KALTCHUK/Z80_Modular_Computer/CPM software/Wordstar/readme.md

## What you'll find in this directory ##
WordStar, an impressive word processor from MicroPro International Corporation. I use it extensively to write all the programs in C, BASIC and assembly language. WSU.COM is the unconfigured version of WordStar. WS.COM is the version I configured for use with VT-100 terminal, 40x80.
