KALTCHUK/Z80_Modular_Computer/CPM software/ZSID/readme.md

## What you'll find in this directory ##
ZSID - Z80 Simbolic Instruction Debugger, from Digital Research. Very useful to debug assembly programs. I used it several times and it saved me many hours. MAKESYM.COM is used to transform .LST file generated by Z80ASM into symbolic tables in a format that ZSID can understand.
