KALTCHUK/Z80_Modular_Computer/pics and vids/backplane_1.jpg

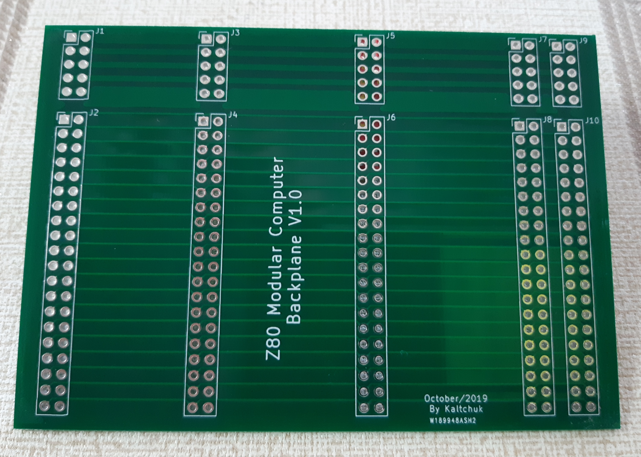
pics and vids/backplane_1.jpg
