KALTCHUK/Z80_Modular_Computer/pics and vids/backplane_3.jpg

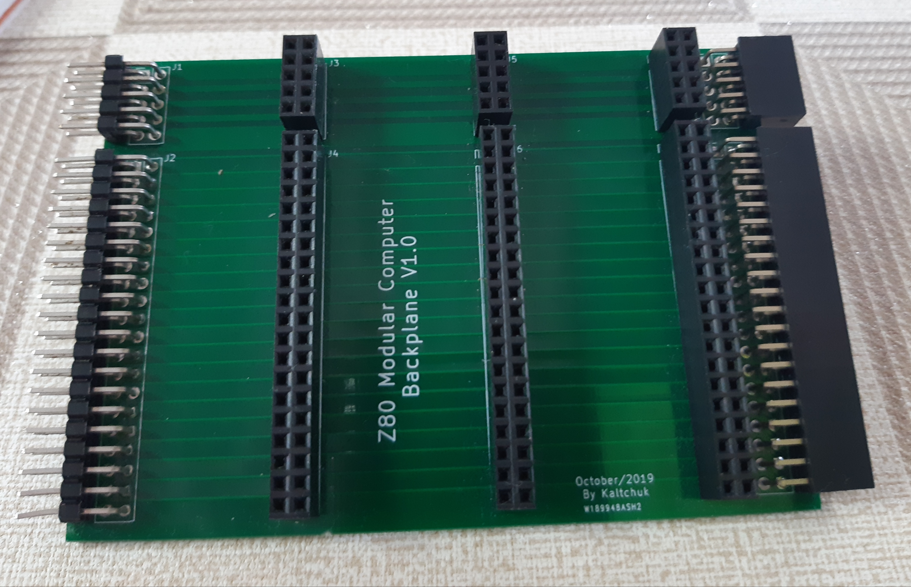
pics and vids/backplane_3.jpg
