KALTCHUK/Z80_Modular_Computer/pics and vids/eprog_1.jpg

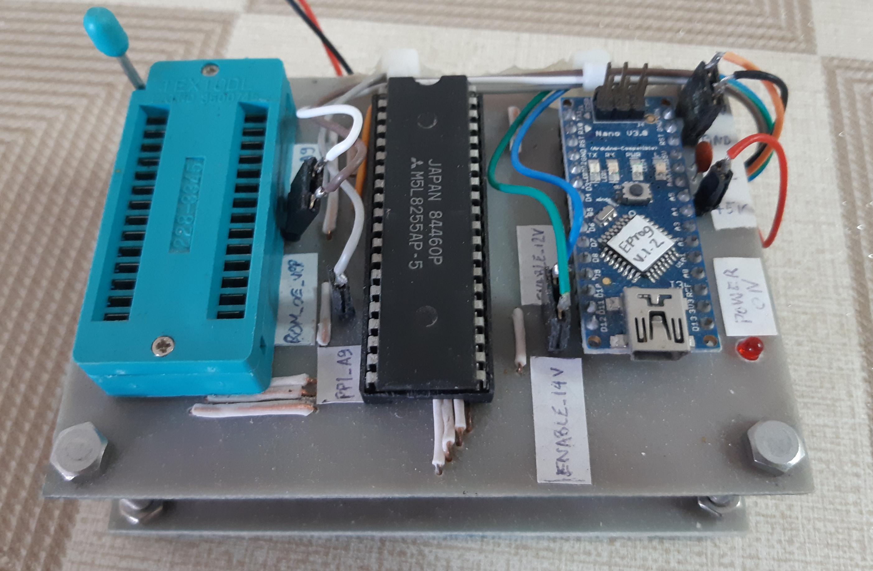
pics and vids/eprog_1.jpg
