KALTCHUK/Z80_Modular_Computer/pics and vids/eprog_2.jpg

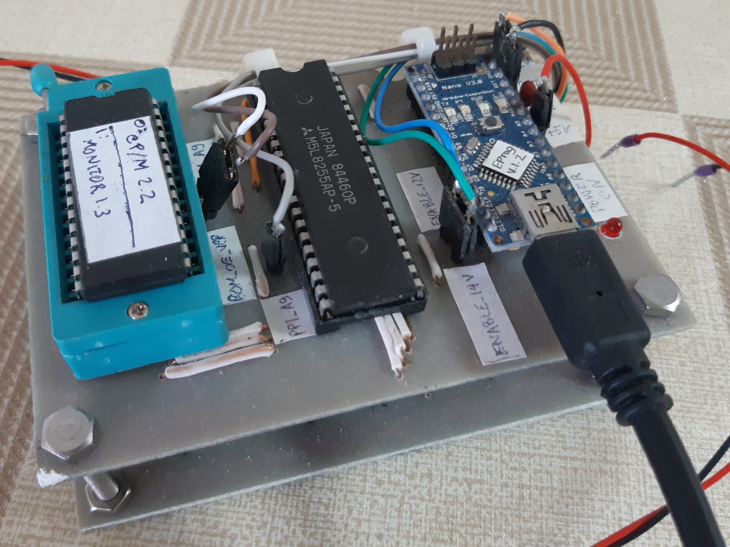
pics and vids/eprog_2.jpg
