KALTCHUK/Z80_Modular_Computer/pics and vids/MANDEL3.png

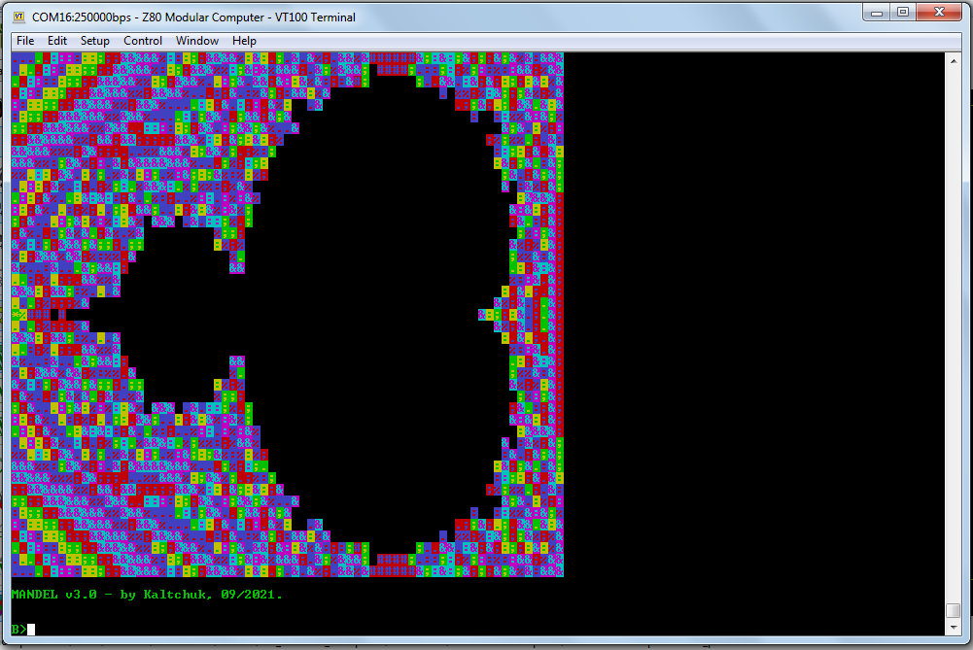
pics and vids/MANDEL3.png
