KALTCHUK/Z80_Modular_Computer/pics and vids/proto_cpu_1.jpg

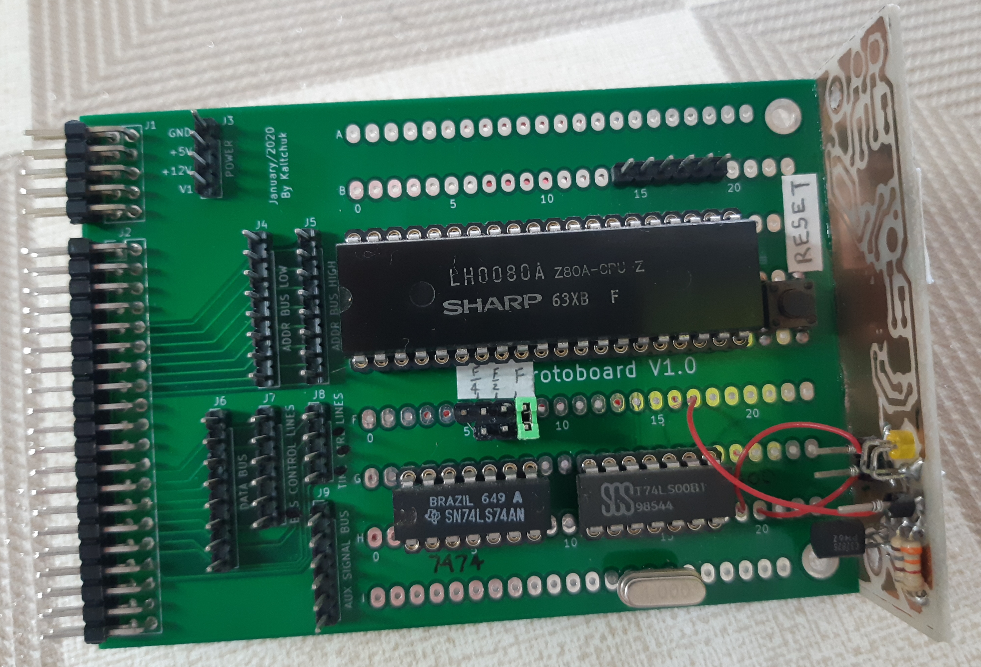
pics and vids/proto_cpu_1.jpg
