KALTCHUK/Z80_Modular_Computer/pics and vids/proto_flash_1.jpg

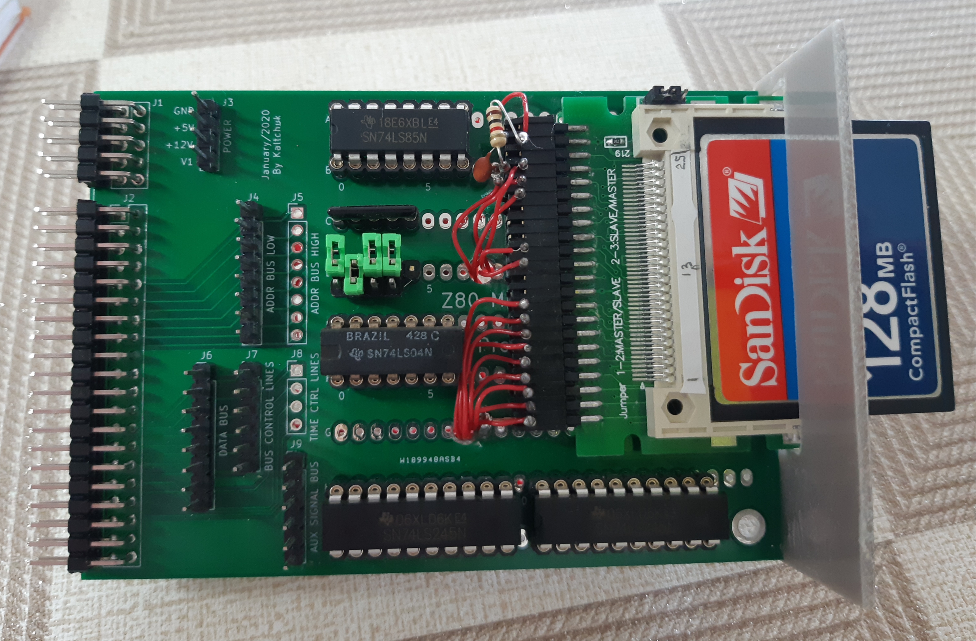
pics and vids/proto_flash_1.jpg
