KALTCHUK/Z80_Modular_Computer/pics and vids/proto_flash_3.jpg

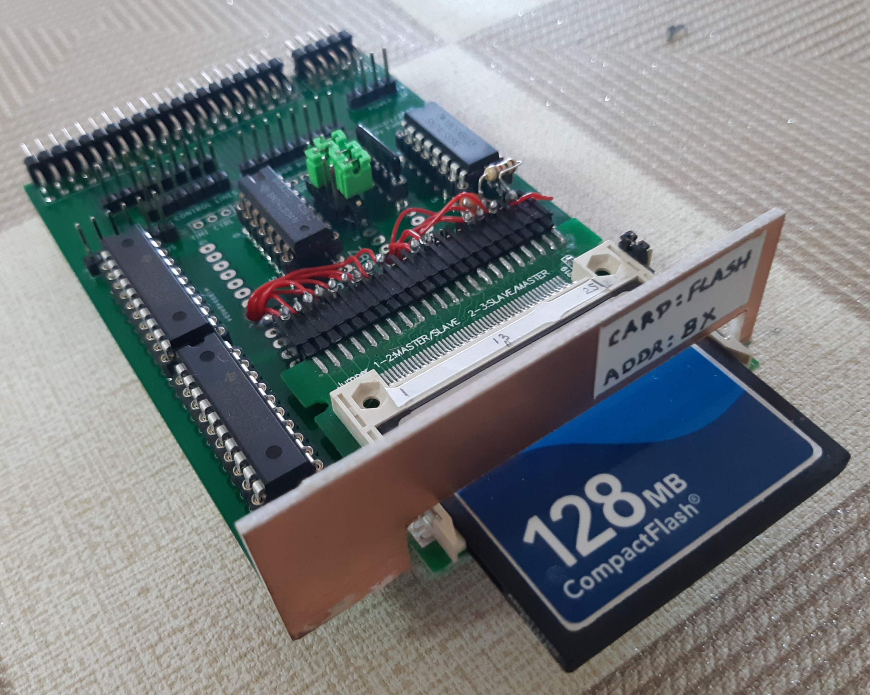
pics and vids/proto_flash_3.jpg
