KALTCHUK/Z80_Modular_Computer/pics and vids/proto_lcd_2.jpg

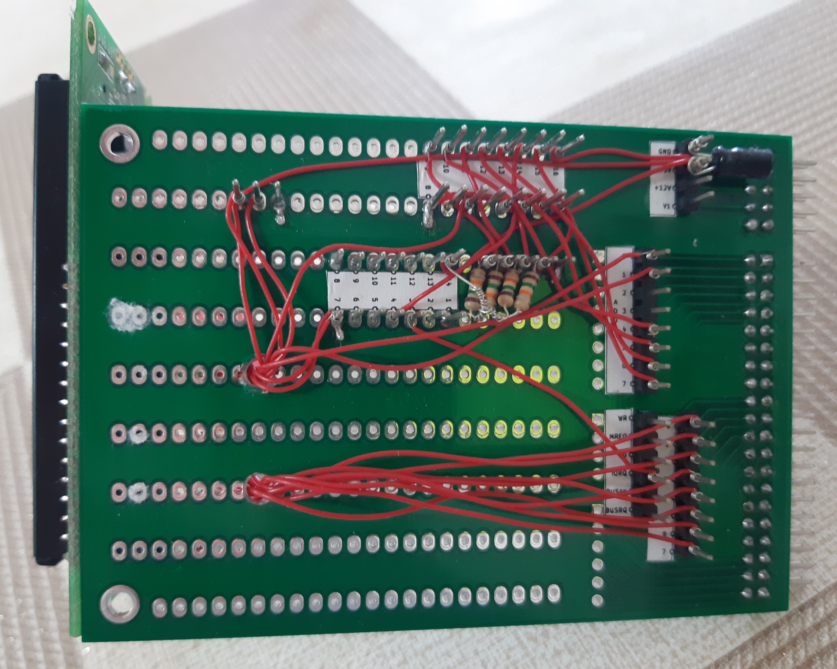
pics and vids/proto_lcd_2.jpg
