KALTCHUK/Z80_Modular_Computer/pics and vids/proto_lcd_3.jpg

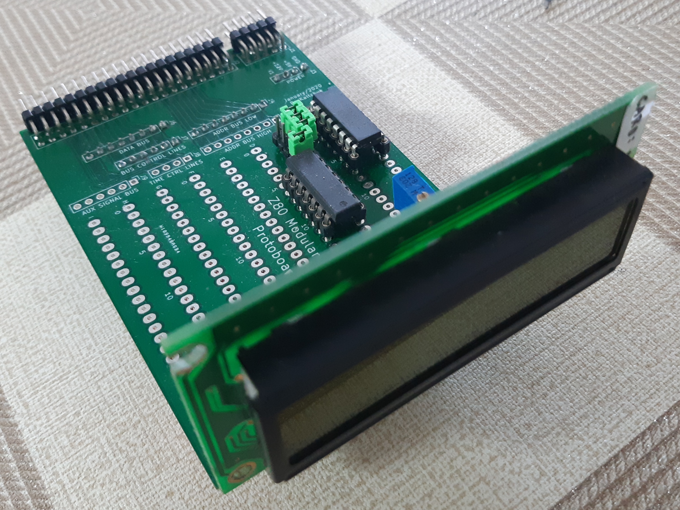
pics and vids/proto_lcd_3.jpg
