KALTCHUK/Z80_Modular_Computer/pics and vids/proto_mem_3.jpg

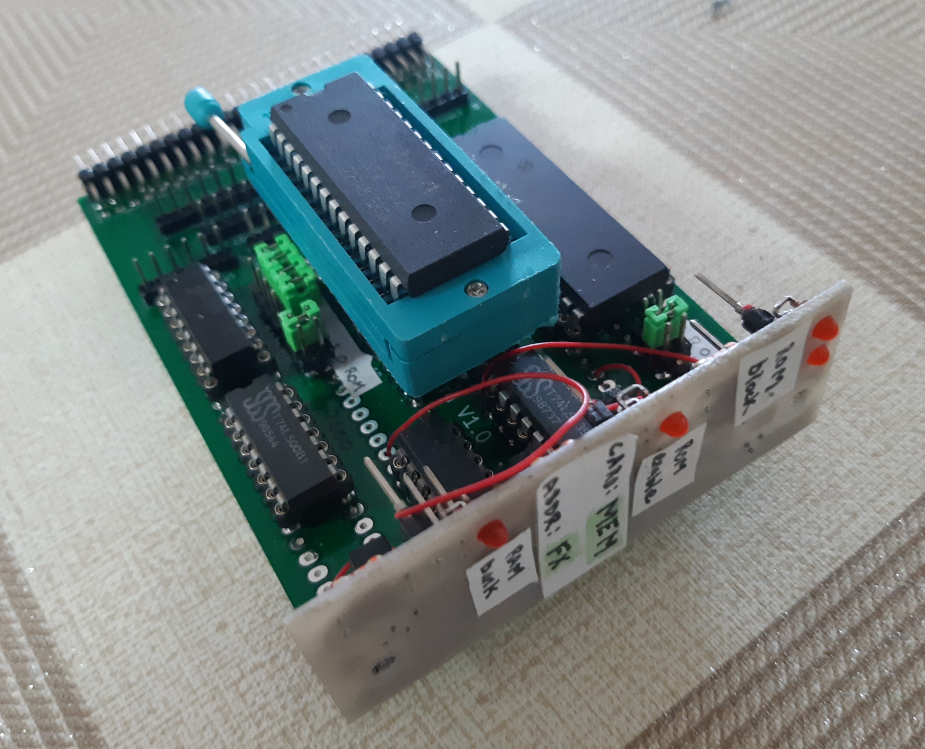
pics and vids/proto_mem_3.jpg
