KALTCHUK/Z80_Modular_Computer/pics and vids/proto_usart_2.jpg

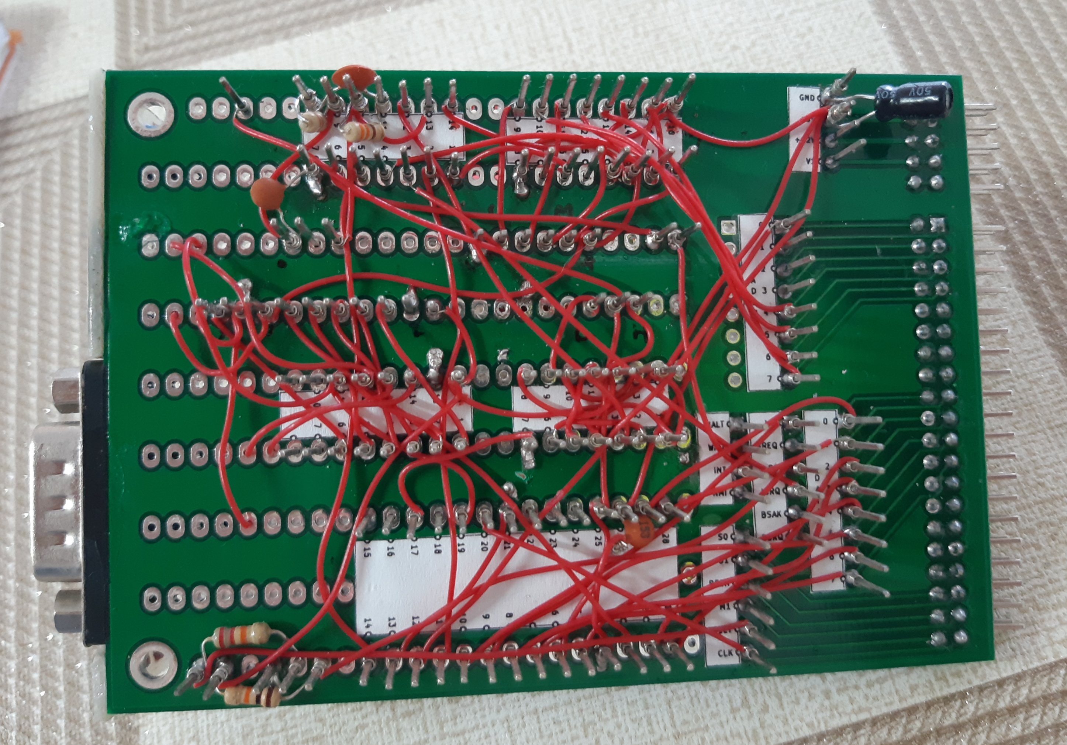
pics and vids/proto_usart_2.jpg
