KALTCHUK/Z80_Modular_Computer/pics and vids/protoboard_2.jpg

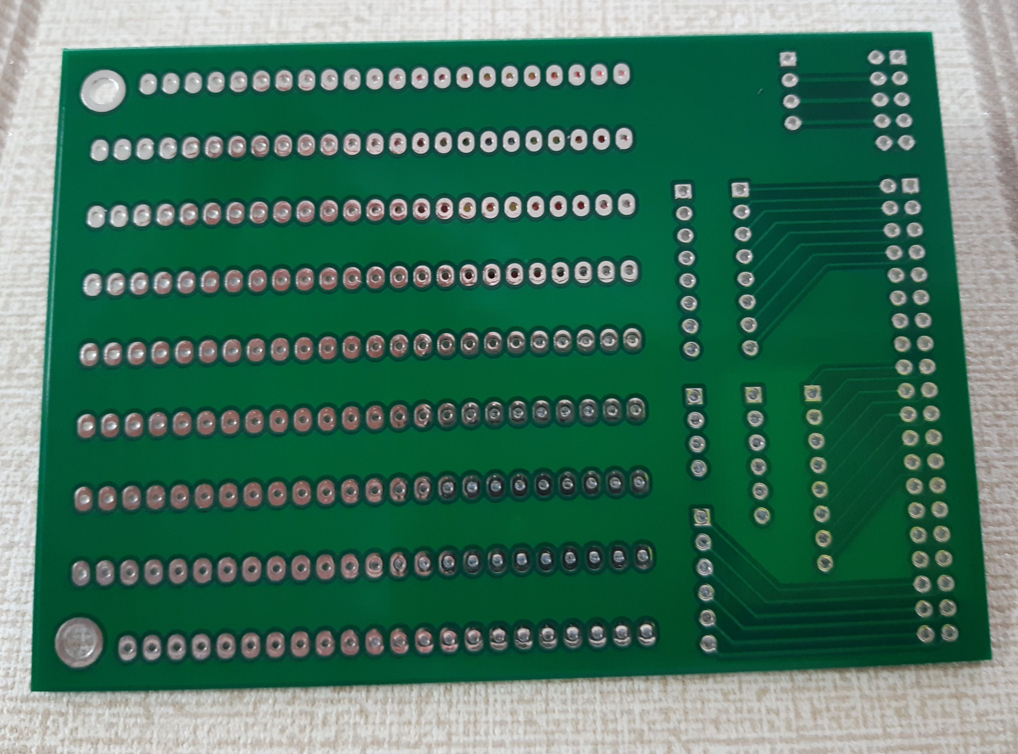
pics and vids/protoboard_2.jpg
