KALTCHUK/Z80_Modular_Computer/pics and vids/assembly_full_3.jpg

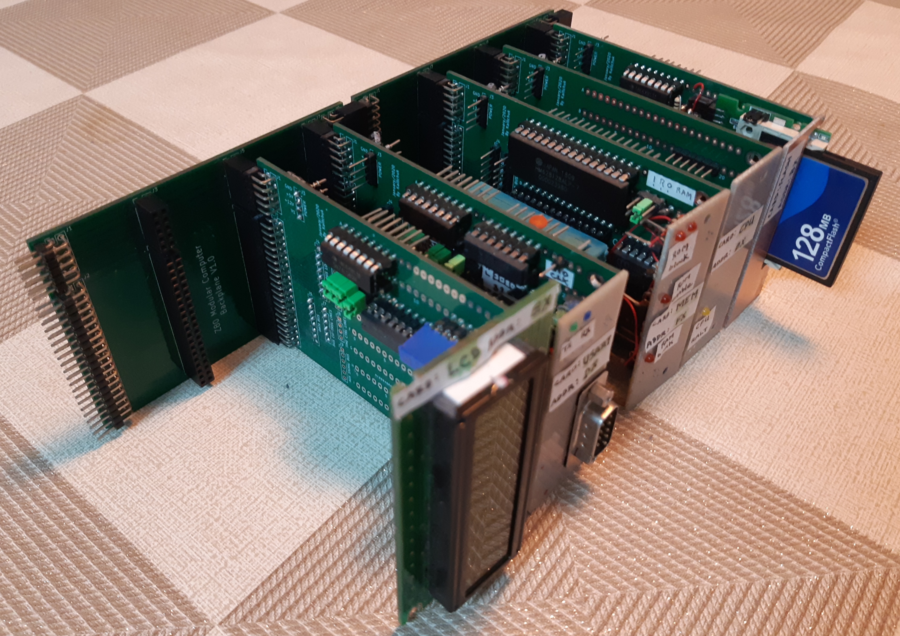
pics and vids/assembly_full_3.jpg
