KALTCHUK/Z80_Modular_Computer/pics and vids/assembly_work_1.jpg

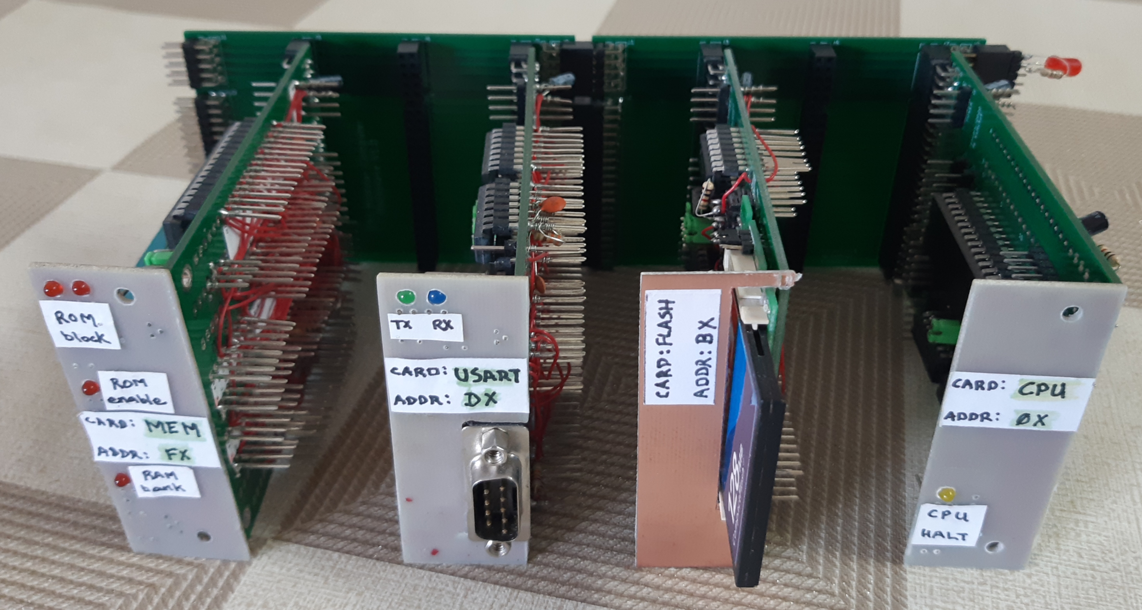
pics and vids/assembly_work_1.jpg
