KALTCHUK/Z80_Modular_Computer/pics and vids/assembly_work_2.jpg

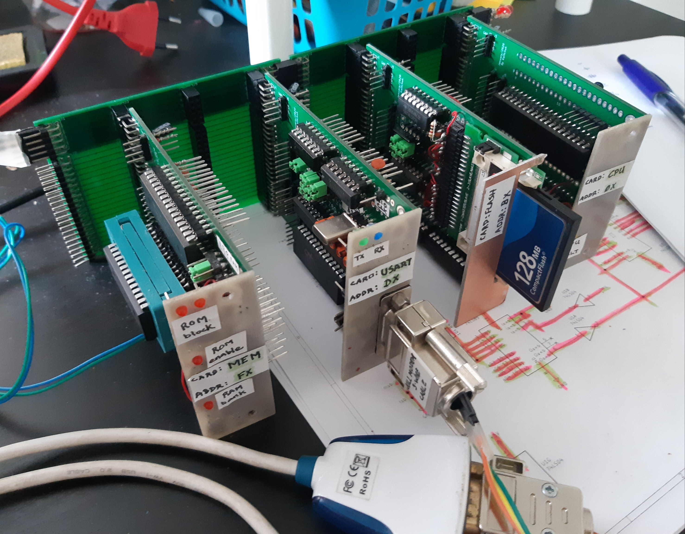
pics and vids/assembly_work_2.jpg
