KALTCHUK/Z80_Modular_Computer/KiCAD files/Proton cards/MEM/MEM-F_Cu.pdf

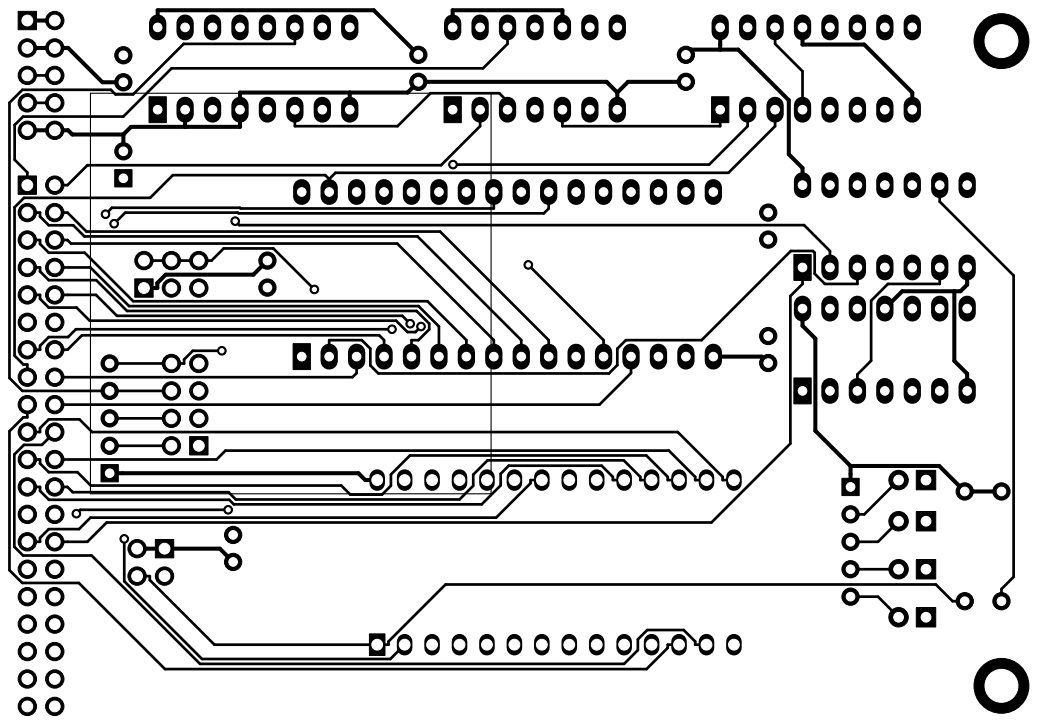
[picture p33: page 1]
