KALTCHUK/Z80_Modular_Computer/KiCAD files/Proton cards/CPU/CPU.pdf

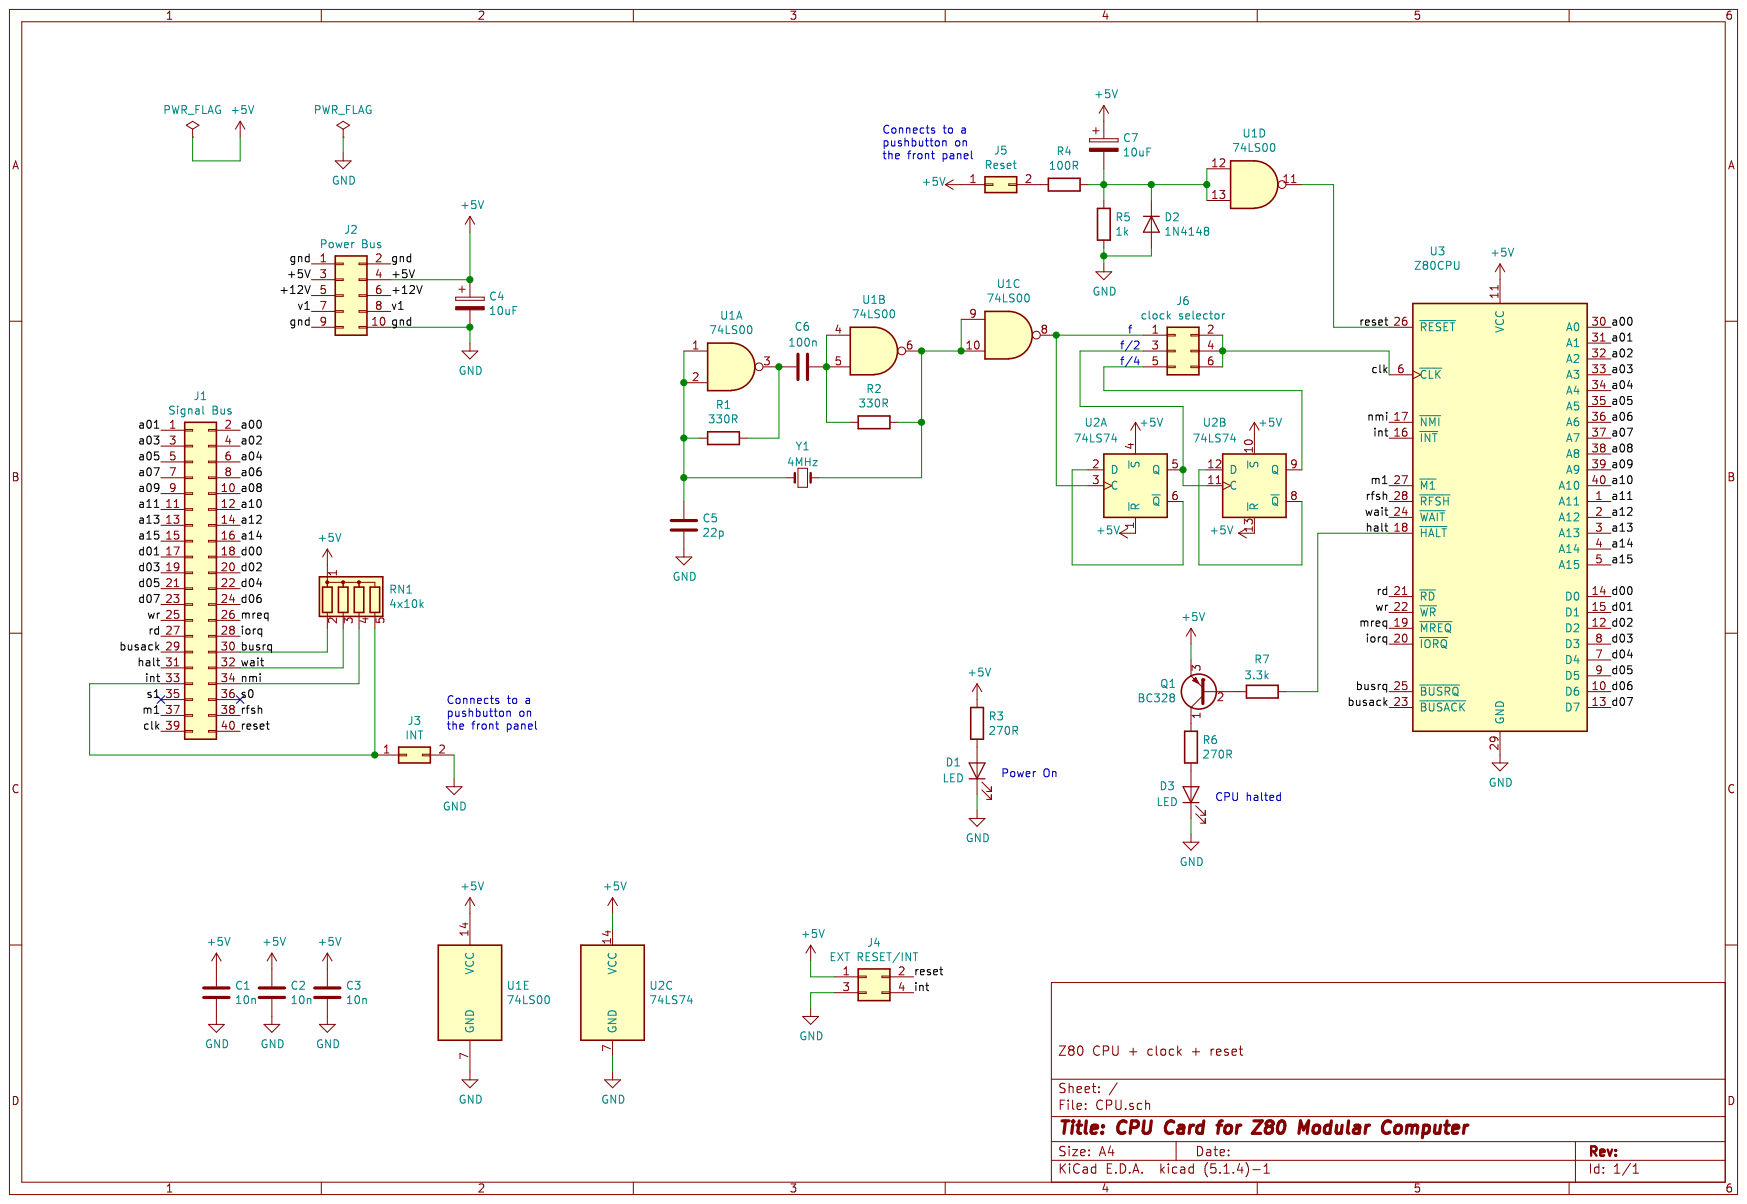
[picture p34: page 1]
