KALTCHUK/Z80_Modular_Computer/KiCAD files/Proton cards/PSU/PSU.kicad_pcb

## KiCad design KiCAD files/Proton cards/PSU/PSU.kicad_pcb (2022-02-26)

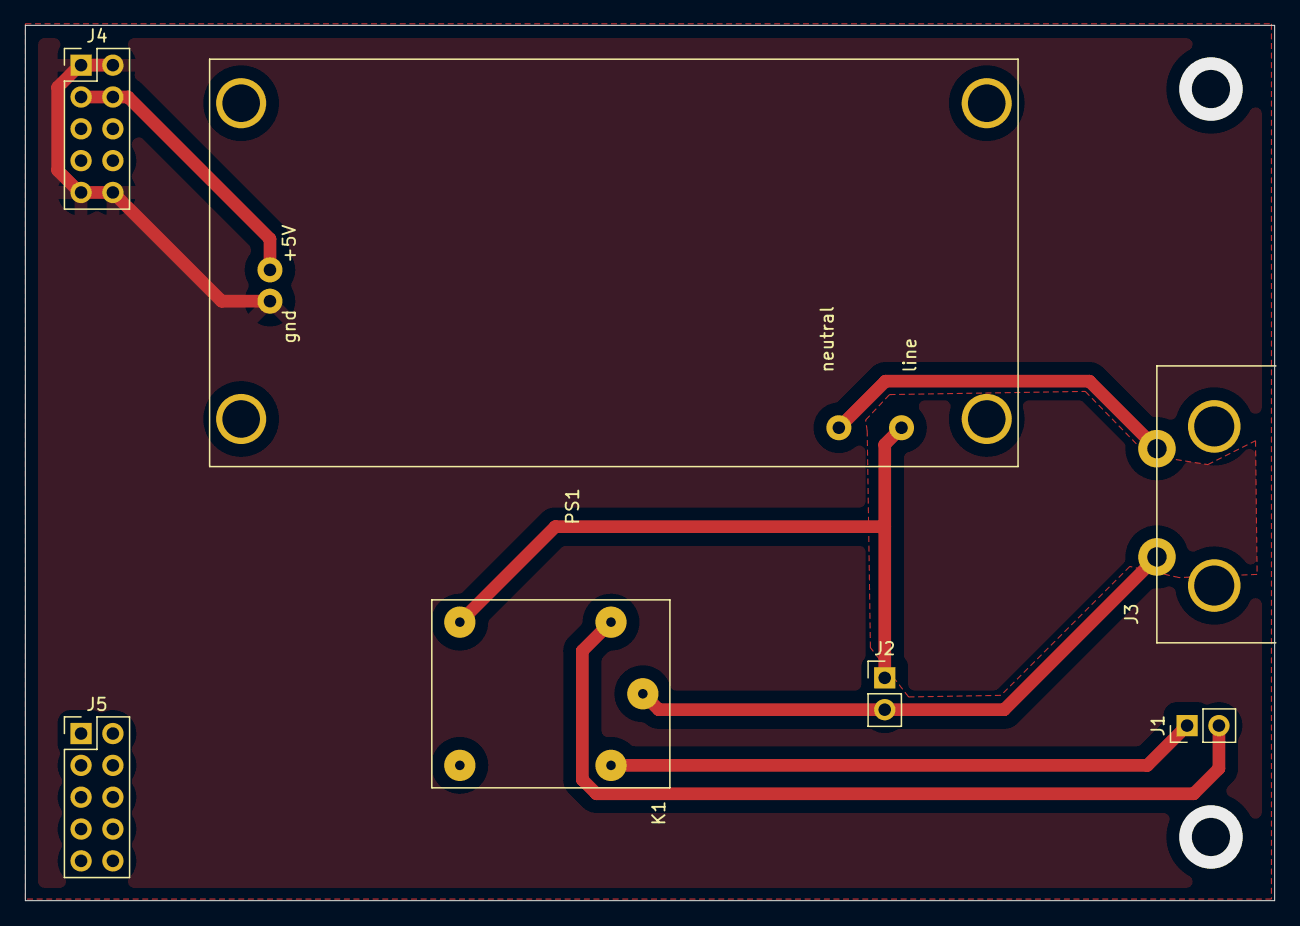
[picture p51: board PSU.kicad_pcb from above]

Board: 2 copper layers, 99.7 x 69.8 mm, 7 parts (0 on the bottom side), 7 nets.

Parts:
J1: Ext power on; PinHeader_1x02_P2.54mm_Vertical
J2: Power switch; PinHeader_1x02_P2.54mm_Vertical
J3: Mains; IEC60320_2pin
J4: Power bus; PinHeader_2x05_P2.54mm_Vertical
J5: Mech support; PinHeader_2x05_P2.54mm_Vertical
K1: SRD-05VDC-SL-C; Relay_SPDT_Songel-15x19mm
PS1: XPJ-01B_5V_10W; Converter_ACDC_5V_10W_XPJ-01B

Connections:
GNDREF: J4.1, J4.2, J4.9, J4.10, PS1.3 (-Vo)
LINE: J2.2, J3.2, K1.5
NEUT: J3.1, PS1.1 (AC/N)
unnamed: J1.1, K1.4
unnamed: J1.2, K1.3
unnamed: J2.1, K1.1, PS1.2 (AC/L)
unnamed: J4.3, J4.4, PS1.4 (+Vo)
