KALTCHUK/Z80_Modular_Computer/KiCAD files/Proton cards/Extension/Extension.kicad_pcb

## KiCad design KiCAD files/Proton cards/Extension/Extension.kicad_pcb (2022-06-04)

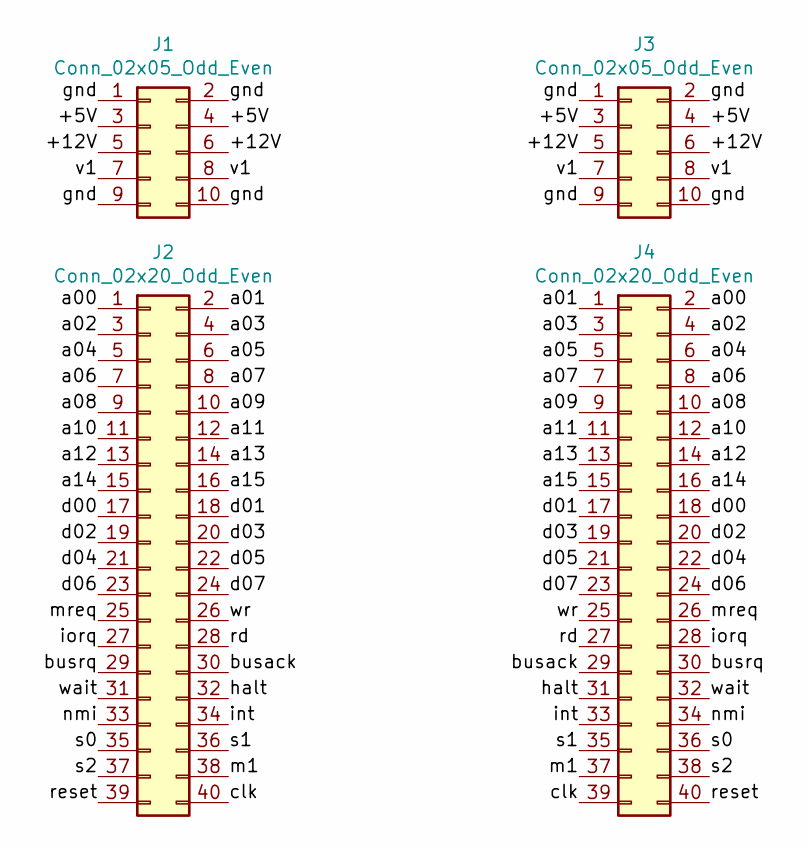
[picture p52: schematic Extension.kicad_sch]

Parts:
J1, J3: Conn_02x05_Odd_Even
J2, J4: Conn_02x20_Odd_Even

Connections:
/+5V: J1.3, J1.4, J3.3, J3.4
/+12V: J1.5, J1.6, J3.5, J3.6
/a00: J2.1, J4.2
/a01: J2.2, J4.1
/a02: J2.3, J4.4
/a03: J2.4, J4.3
/a04: J2.5, J4.6
/a05: J2.6, J4.5
/a06: J2.7, J4.8
/a07: J2.8, J4.7
/a08: J2.9, J4.10
/a09: J2.10, J4.9
/a10: J2.11, J4.12
/a11: J2.12, J4.11
/a12: J2.13, J4.14
/a13: J2.14, J4.13
/a14: J2.15, J4.16
/a15: J2.16, J4.15
/busack: J2.30, J4.29
/busrq: J2.29, J4.30
/clk: J2.40, J4.39
/d00: J2.17, J4.18
/d01: J2.18, J4.17
/d02: J2.19, J4.20
/d03: J2.20, J4.19
/d04: J2.21, J4.22
/d05: J2.22, J4.21
/d06: J2.23, J4.24
/d07: J2.24, J4.23
/gnd: J1.1, J1.2, J1.9, J1.10, J3.1, J3.2, J3.9, J3.10
/halt: J2.32, J4.31
/int: J2.34, J4.33
/iorq: J2.27, J4.28
/m1: J2.38, J4.37
/mreq: J2.25, J4.26
/nmi: J2.33, J4.34
/rd: J2.28, J4.27
/reset: J2.39, J4.40
/s0: J2.35, J4.36
/s1: J2.36, J4.35
/s2: J2.37, J4.38
/v1: J1.7, J1.8, J3.7, J3.8
/wait: J2.31, J4.32
/wr: J2.26, J4.25

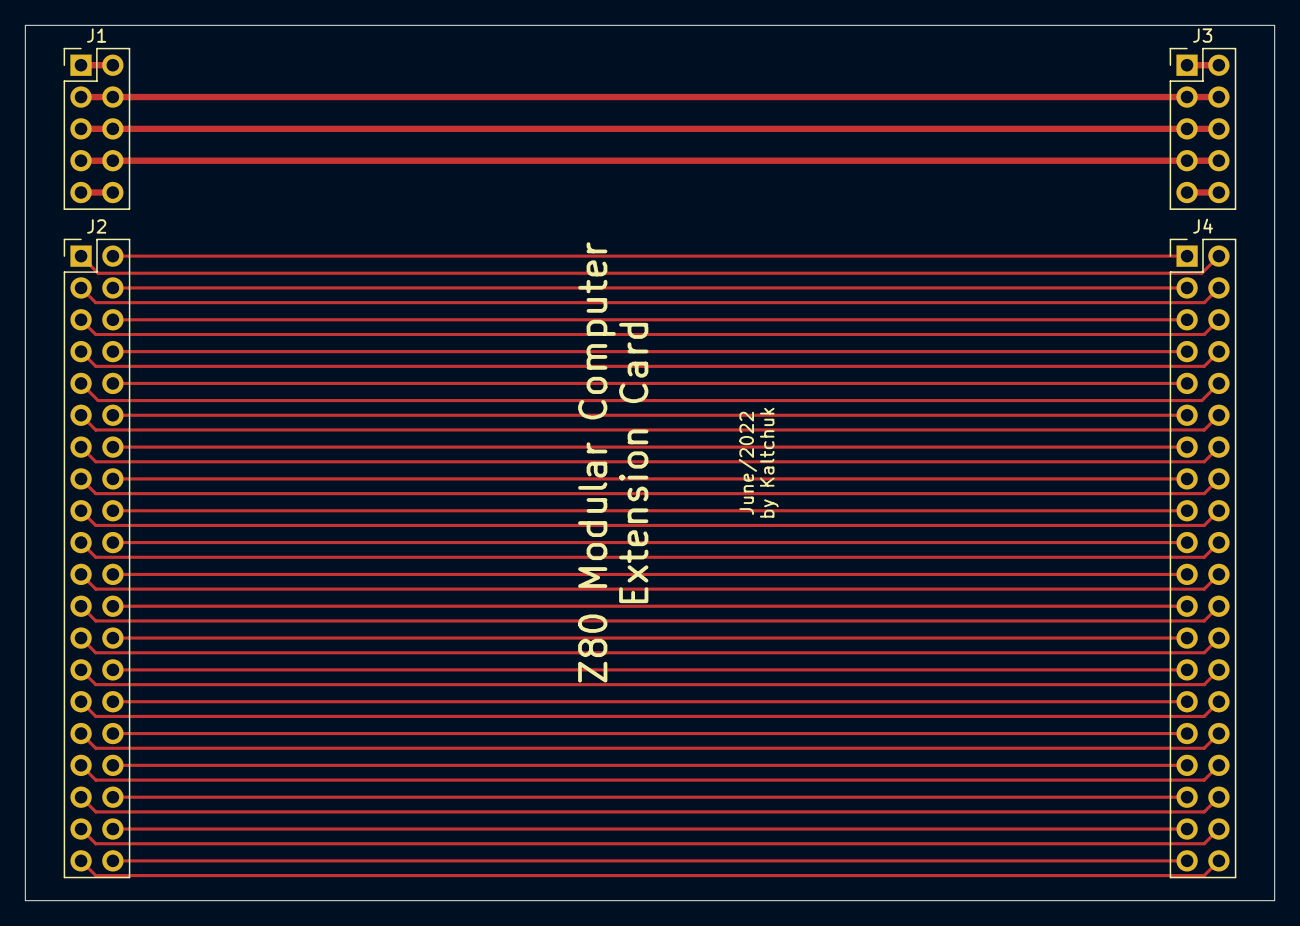
[picture p53: board Extension.kicad_pcb from above]

Board: 2 copper layers, 99.7 x 69.8 mm, 4 parts (0 on the bottom side), 44 nets.
