KALTCHUK/Z80_Modular_Computer/KiCAD files/Proton cards/PX051/Px051_frontal/Px051_frontal.kicad_pcb

## KiCad design KiCAD files/Proton cards/PX051/Px051_frontal/Px051_frontal.kicad_pcb (2022-03-13)

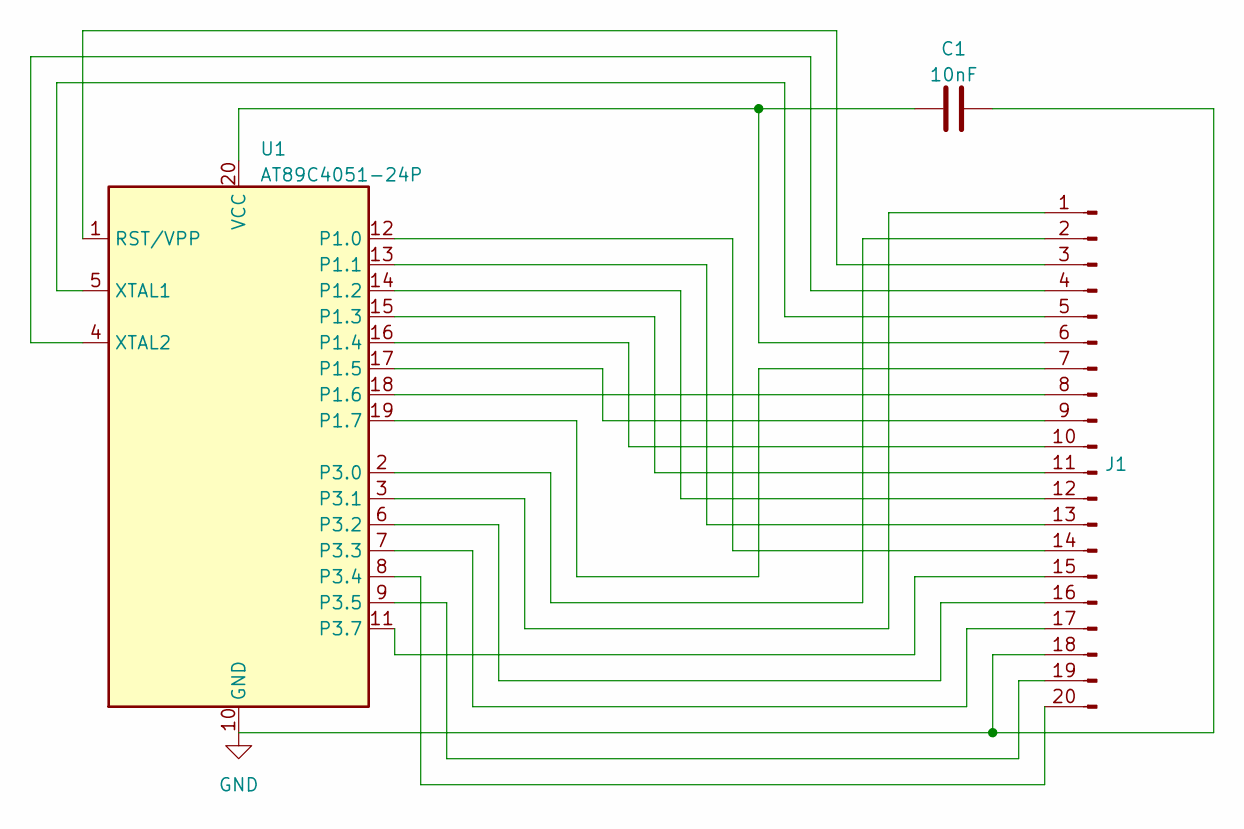
[picture p54: schematic Px051_frontal.kicad_sch]

Parts:
C1: 10nF; C_Disc_D3.0mm_W2.0mm_P2.50mm
J1: Conn_01x20_Male; PinHeader_1x20_P2.54mm_Vertical
U1: AT89C4051-24P; DIP-20_W7.62mm_Socket_LongPads

Connections:
GND: C1.2, J1.18, U1.10 (GND)
unnamed: C1.1, J1.6, U1.20 (VCC)
unnamed: J1.1, U1.3 (P3.1)
unnamed: J1.2, U1.2 (P3.0)
unnamed: J1.3, U1.1 (RST/VPP)
unnamed: J1.4, U1.4 (XTAL2)
unnamed: J1.5, U1.5 (XTAL1)
unnamed: J1.7, U1.19 (P1.7)
unnamed: J1.8, U1.18 (P1.6)
unnamed: J1.9, U1.17 (P1.5)
unnamed: J1.10, U1.16 (P1.4)
unnamed: J1.11, U1.15 (P1.3)
unnamed: J1.12, U1.14 (P1.2)
unnamed: J1.13, U1.13 (P1.1)
unnamed: J1.14, U1.12 (P1.0)
unnamed: J1.15, U1.11 (P3.7)
unnamed: J1.16, U1.6 (P3.2)
unnamed: J1.17, U1.7 (P3.3)
unnamed: J1.19, U1.9 (P3.5)
unnamed: J1.20, U1.8 (P3.4)
