KALTCHUK/Z80_Modular_Computer/KiCAD files/Proton cards/PX051/Px051_frontal/Px051_frontal.kicad_pcb

## KiCad design KiCAD files/Proton cards/PX051/Px051_frontal/Px051_frontal.kicad_pcb (continued)

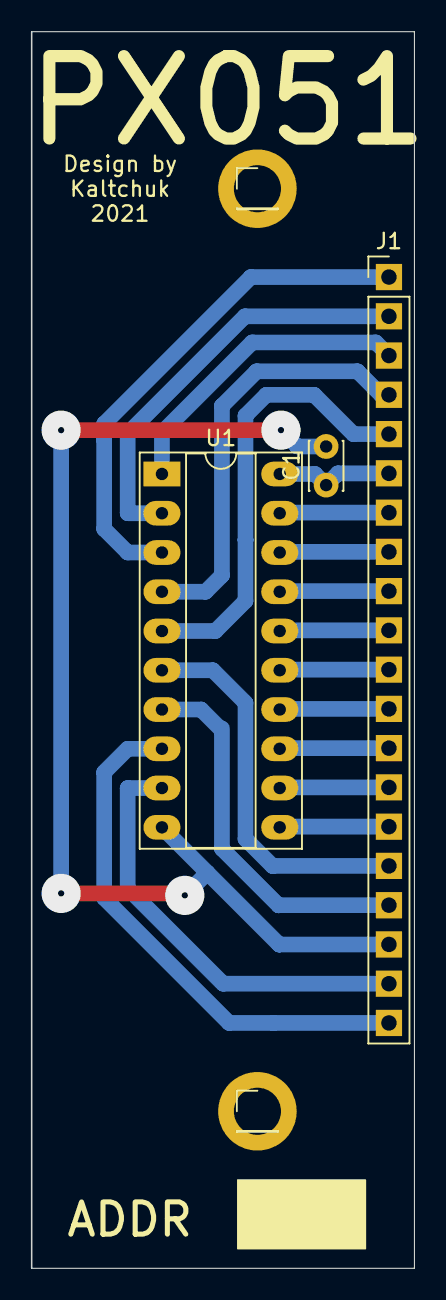
[picture p55: board Px051_frontal.kicad_pcb from above]

Board: 2 copper layers, 24.8 x 80.0 mm, 5 parts (0 on the bottom side), 20 nets.

Other parts of the board:
J7, J8: fixing bolt; PinHeader_1x01_P2.54mm_Vertical
