KALTCHUK/Z80_Modular_Computer/KiCAD files/EProg/EProg.kicad_pcb

## KiCad design KiCAD files/EProg/EProg.kicad_pcb (2020-09-26)

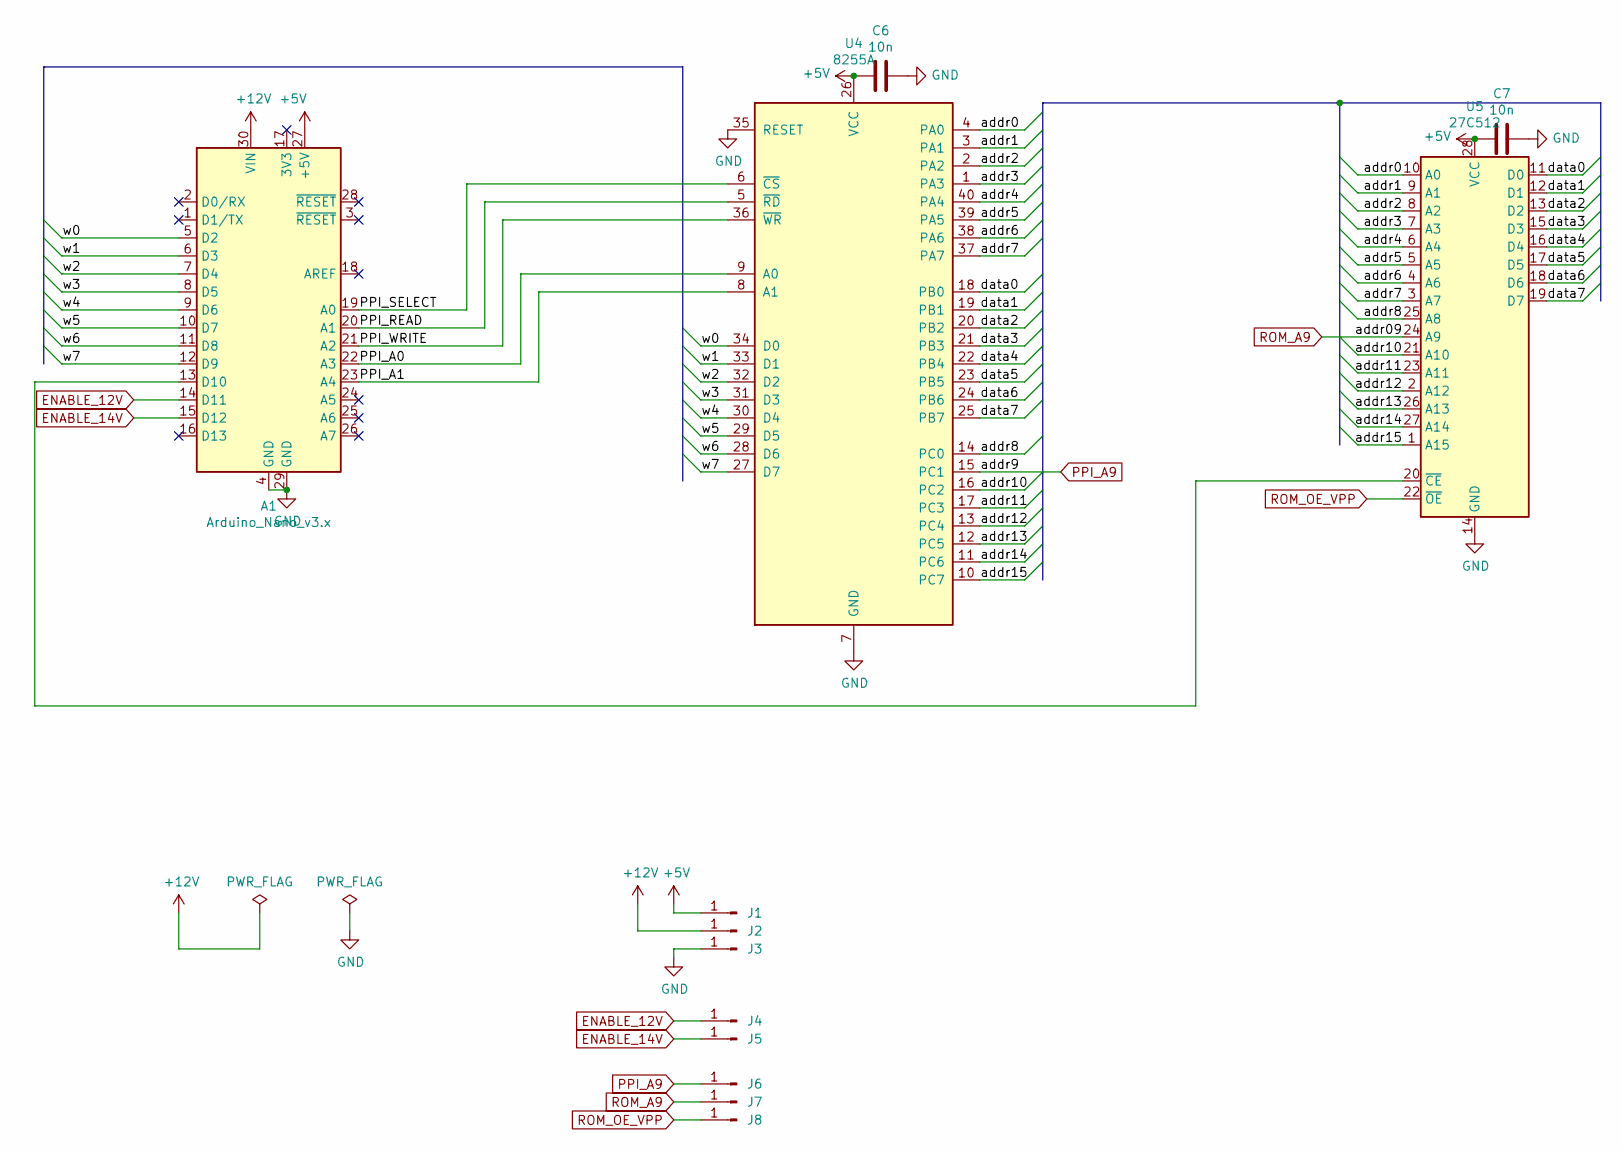
[picture p56: schematic EProg.kicad_sch, EEPROM (W27C512) Programmer]

Parts:
A1: Arduino_Nano_v3.x; Arduino_Nano
C6, C7: 10n; C_Disc_D3.0mm_W2.0mm_P2.50mm
J1, J2, J3, J4, J5, J6, J7, J8: Conn_01x01_Male; PinHeader_1x01_P2.54mm_Vertical
U4: 8255A; DIP-40_W15.24mm
U5: 27C512; DIP-28_W15.24mm

Connections:
+5V: A1.27 (+5V), C6.1, C7.1, J1.1, U4.26 (VCC), U5.28 (VCC)
+12V: A1.30 (VIN), J2.1
/PPI_A0: A1.22 (A3), U4.9 (A0)
/PPI_A1: A1.23 (A4), U4.8 (A1)
/PPI_READ: A1.20 (A1), U4.5 (~RD)
/PPI_SELECT: A1.19 (A0), U4.6 (~CS)
/PPI_WRITE: A1.21 (A2), U4.36 (~WR)
/addr0: U4.4 (PA0), U5.10 (A0)
/addr1: U4.3 (PA1), U5.9 (A1)
/addr2: U4.2 (PA2), U5.8 (A2)
/addr3: U4.1 (PA3), U5.7 (A3)
/addr4: U4.40 (PA4), U5.6 (A4)
/addr5: U4.39 (PA5), U5.5 (A5)
/addr6: U4.38 (PA6), U5.4 (A6)
/addr7: U4.37 (PA7), U5.3 (A7)
/addr8: U4.14 (PC0), U5.25 (A8)
/addr10: U4.16 (PC2), U5.21 (A10)
/addr11: U4.17 (PC3), U5.23 (A11)
/addr12: U4.13 (PC4), U5.2 (A12)
/addr13: U4.12 (PC5), U5.26 (A13)
/addr14: U4.11 (PC6), U5.27 (A14)
/addr15: U4.10 (PC7), U5.1 (A15)
/data0: U4.18 (PB0), U5.11 (D0)
/data1: U4.19 (PB1), U5.12 (D1)
/data2: U4.20 (PB2), U5.13 (D2)
/data3: U4.21 (PB3), U5.15 (D3)
/data4: U4.22 (PB4), U5.16 (D4)
/data5: U4.23 (PB5), U5.17 (D5)
/data6: U4.24 (PB6), U5.18 (D6)
/data7: U4.25 (PB7), U5.19 (D7)
/w0: A1.5 (D2), U4.34 (D0)
/w1: A1.6 (D3), U4.33 (D1)
/w2: A1.7 (D4), U4.32 (D2)
/w3: A1.8 (D5), U4.31 (D3)
/w4: A1.9 (D6), U4.30 (D4)
/w5: A1.10 (D7), U4.29 (D5)
/w6: A1.11 (D8), U4.28 (D6)
/w7: A1.12 (D9), U4.27 (D7)
ENABLE_12V: A1.14 (D11), J4.1
ENABLE_14V: A1.15 (D12), J5.1
GND: A1.4 (GND), A1.29 (GND), C6.2, C7.2, J3.1, U4.7 (GND), U4.35 (RESET), U5.14 (GND)
unnamed: A1.13 (D10), U5.20 (~CE)
PPI_A9: J6.1, U4.15 (PC1)
ROM_A9: J7.1, U5.24 (A9)
ROM_OE_VPP: J8.1, U5.22 (~OE)

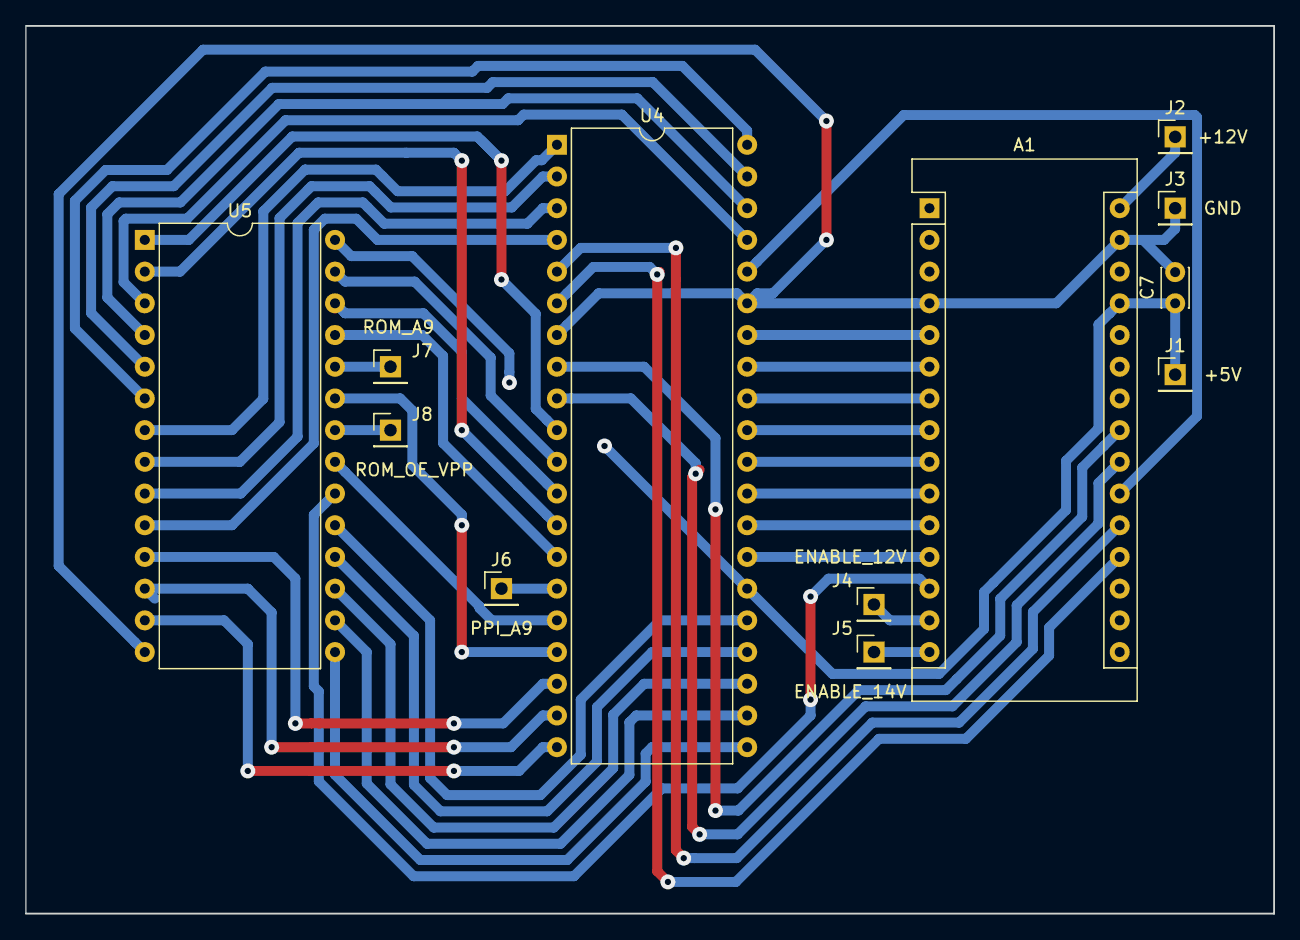
[picture p57: board EProg.kicad_pcb from above]

Board: 2 copper layers, 100.0 x 71.1 mm, 12 parts (0 on the bottom side), 45 nets.
