KALTCHUK/Z80_Modular_Computer/KiCAD files/EProg/EProg (discrete part)/EProg (discrete part).kicad_pcb

## KiCad design KiCAD files/EProg/EProg (discrete part)/EProg (discrete part).kicad_pcb (2020-09-26)

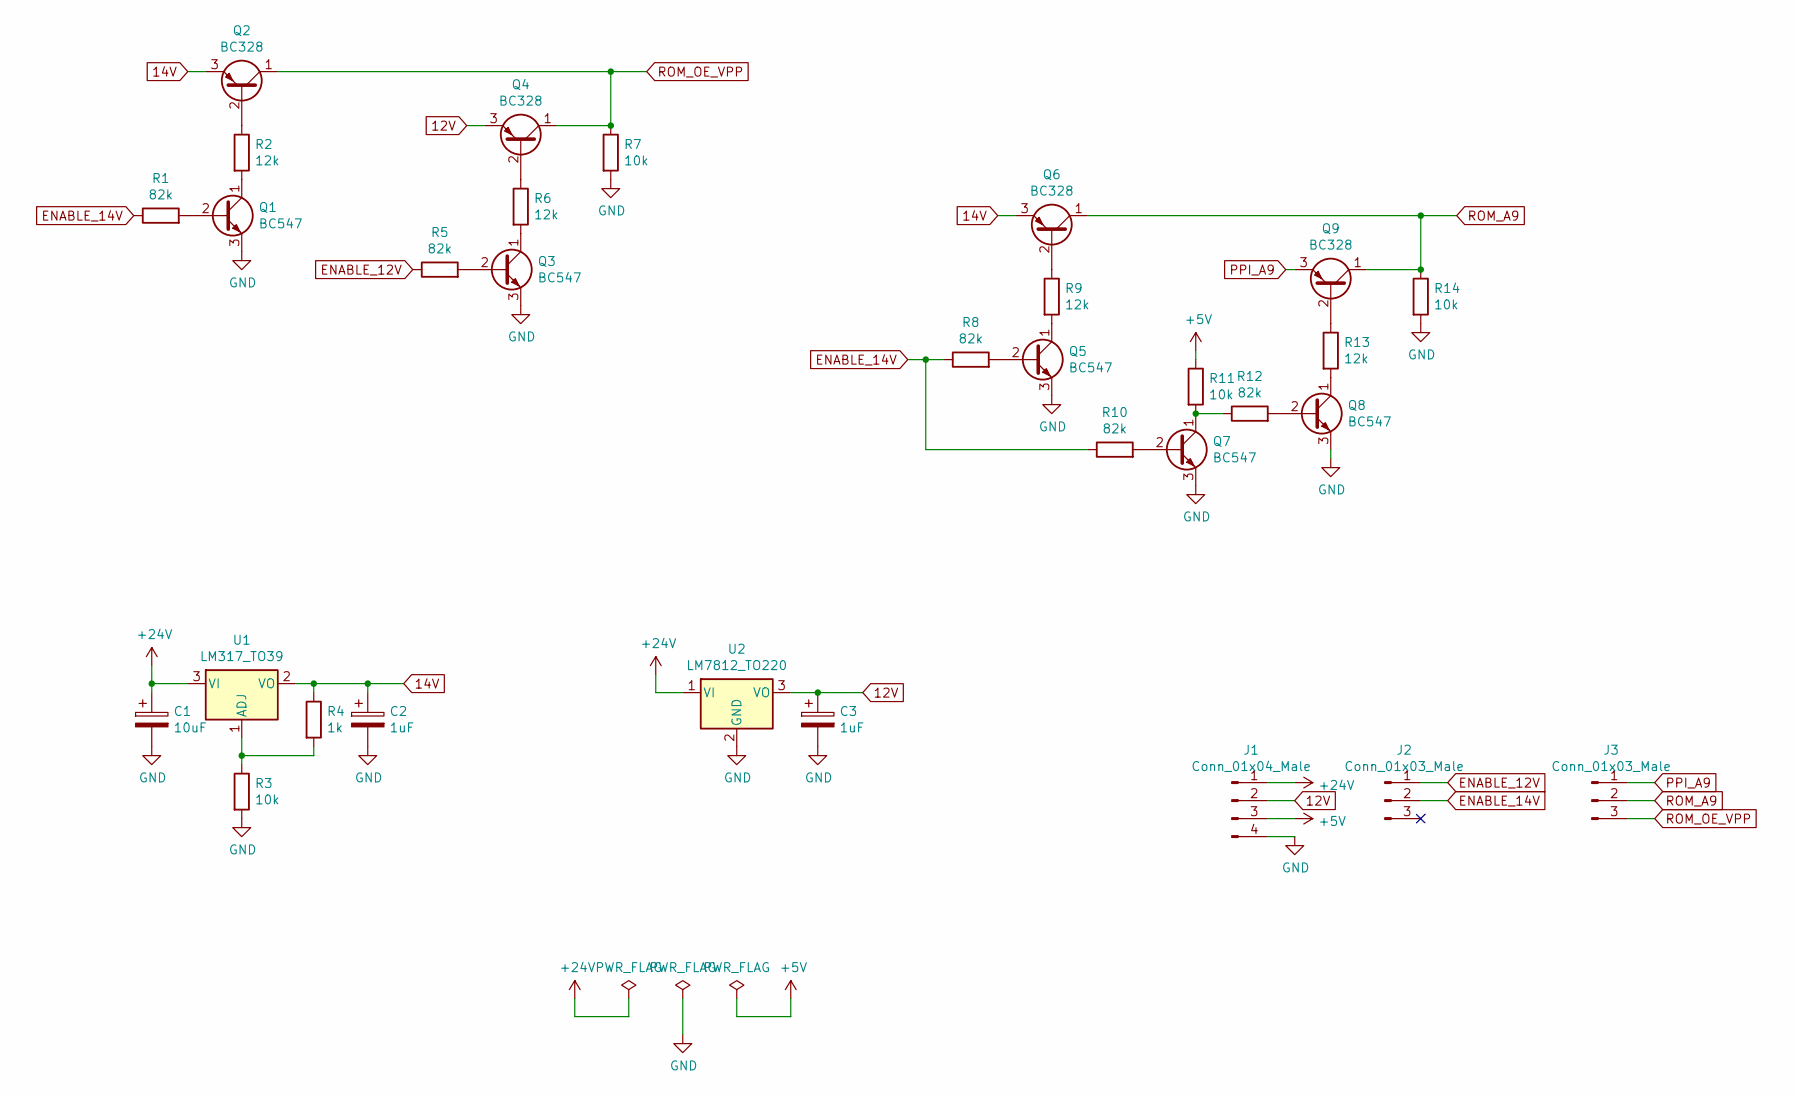
[picture p58: schematic EProg (discrete part).kicad_sch]

Parts:
C1: 10uF; CP_Radial_D5.0mm_P2.50mm
C2, C3: 1uF; CP_Radial_D5.0mm_P2.50mm
J1: Conn_01x04_Male; PinHeader_1x04_P2.54mm_Horizontal
J2, J3: Conn_01x03_Male; PinHeader_1x03_P2.54mm_Horizontal
Q1, Q3, Q5, Q7, Q8: BC547; TO-92_Inline
Q2, Q4, Q6, Q9: BC328; TO-92_Inline
R1, R5, R8, R10, R12: 82k; R_Axial_DIN0207_L6.3mm_D2.5mm_P7.62mm_Horizontal
R2, R6, R9, R13: 12k; R_Axial_DIN0207_L6.3mm_D2.5mm_P7.62mm_Horizontal
R3, R7, R11, R14: 10k; R_Axial_DIN0207_L6.3mm_D2.5mm_P7.62mm_Horizontal
R4: 1k; R_Axial_DIN0207_L6.3mm_D2.5mm_P7.62mm_Horizontal
U1: LM317_TO39; TO-39-3
U2: LM7812_TO220; TO-220-3_Vertical

Connections:
12V: C3.1, J1.2, Q4.3 (E), U2.3 (VO)
14V: C2.1, Q2.3 (E), Q6.3 (E), R4.1, U1.2 (VO)
+5V: J1.3, R11.1
+24V: C1.1, J1.1, U1.3 (VI), U2.1 (VI)
ENABLE_12V: J2.1, R5.1
ENABLE_14V: J2.2, R1.1, R8.1, R10.1
GND: C1.2, C2.2, C3.2, J1.4, Q1.3 (E), Q3.3 (E), Q5.3 (E), Q7.3 (E), Q8.3 (E), R3.2, R7.2, R14.2, U2.2 (GND)
unnamed: Q1.1 (C), R2.2
unnamed: Q1.2 (B), R1.2
unnamed: Q2.2 (B), R2.1
unnamed: Q3.1 (C), R6.2
unnamed: Q3.2 (B), R5.2
unnamed: Q4.2 (B), R6.1
unnamed: Q5.1 (C), R9.2
unnamed: Q5.2 (B), R8.2
unnamed: Q6.2 (B), R9.1
unnamed: Q7.1 (C), R11.2, R12.1
unnamed: Q7.2 (B), R10.2
unnamed: Q8.1 (C), R13.2
unnamed: Q8.2 (B), R12.2
unnamed: Q9.2 (B), R13.1
unnamed: R3.1, R4.2, U1.1 (ADJ)
PPI_A9: J3.1, Q9.3 (E)
ROM_A9: J3.2, Q6.1 (C), Q9.1 (C), R14.1
ROM_OE_VPP: J3.3, Q2.1 (C), Q4.1 (C), R7.1

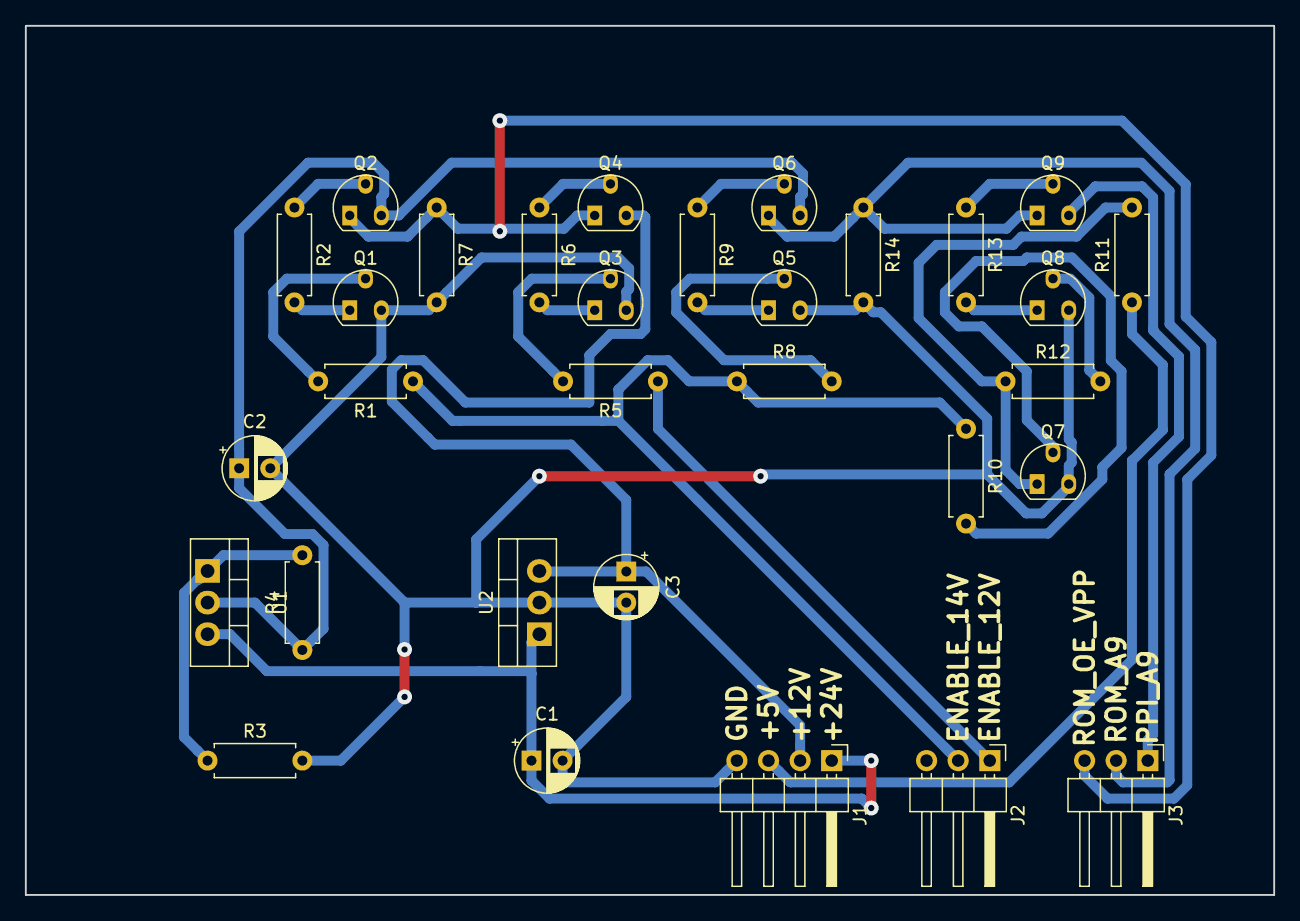
[picture p59: board EProg (discrete part).kicad_pcb from above]

Board: 2 copper layers, 100.3 x 69.8 mm, 31 parts (0 on the bottom side), 25 nets.
