KALTCHUK/Z80_Modular_Computer/KiCAD files/PLC cards/DO-08/DO-08.kicad_sch

## KiCad design KiCAD files/PLC cards/DO-08/DO-08.kicad_sch (2023-01-21)

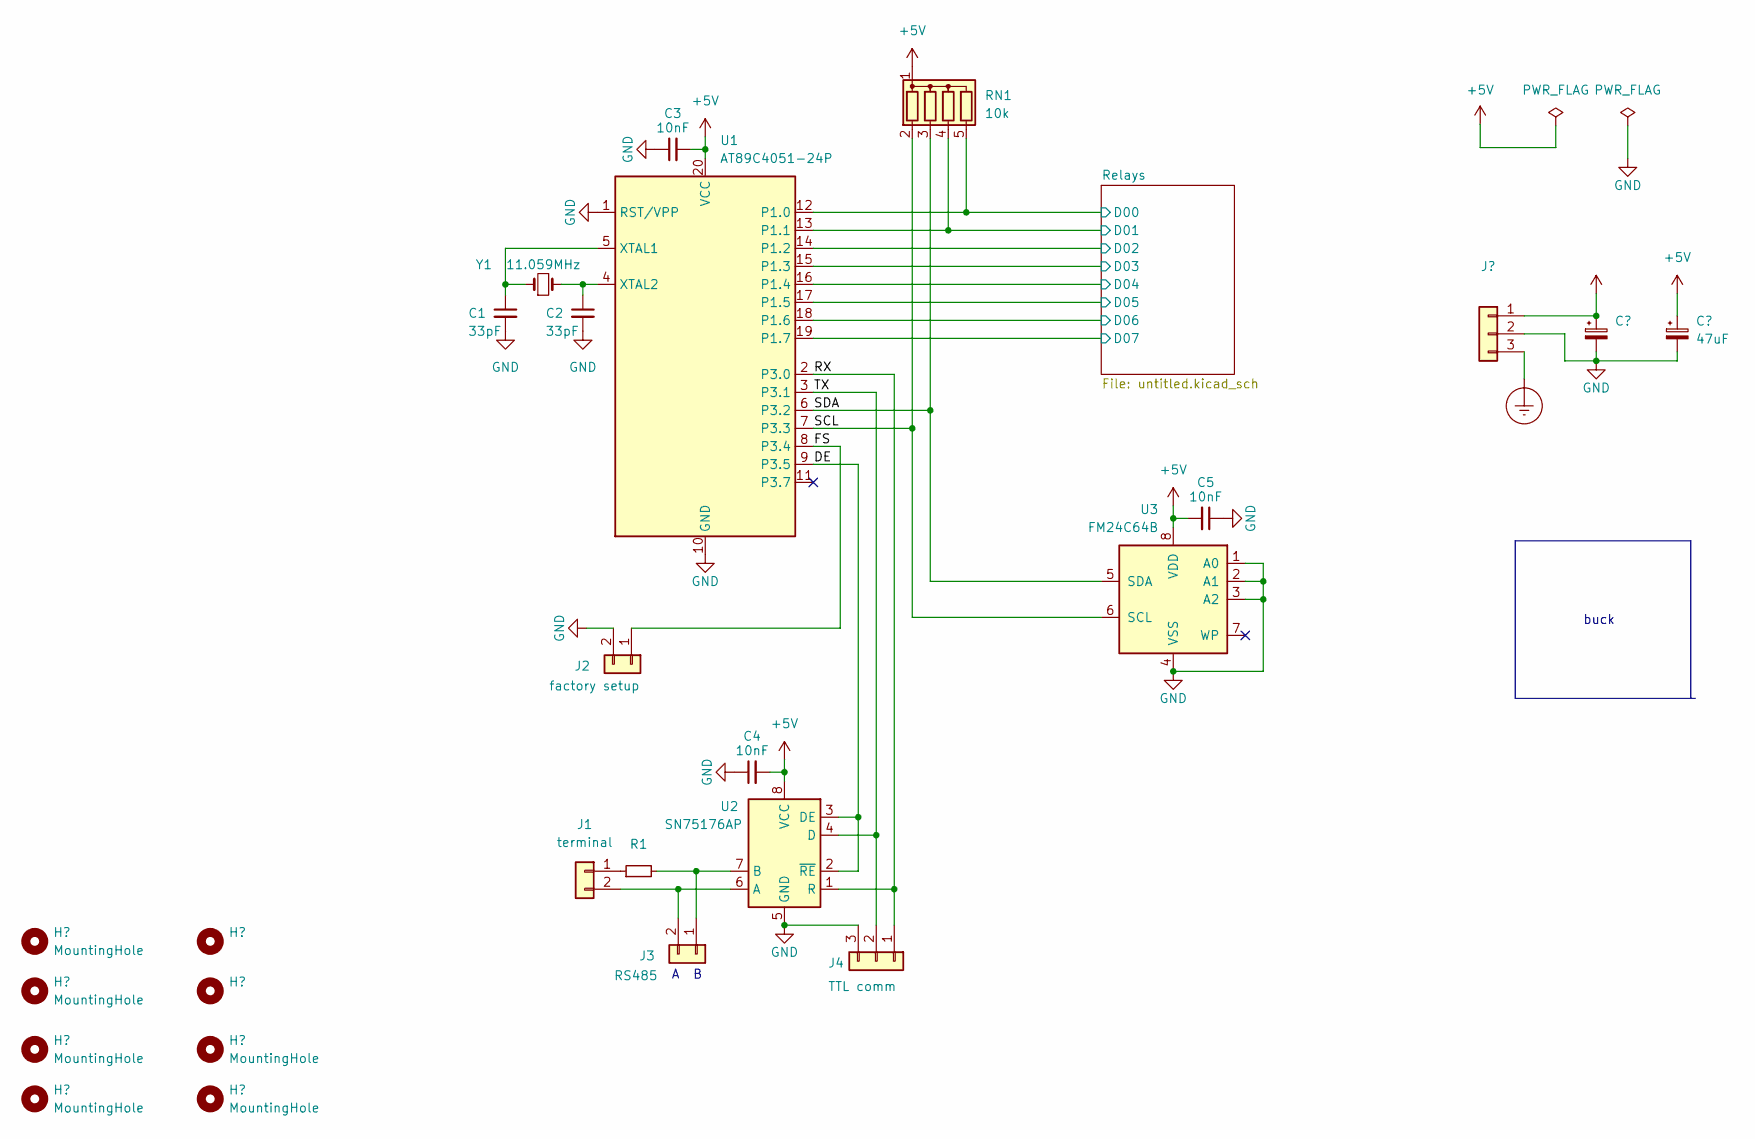
[picture p60: schematic DO-08.kicad_sch]

Parts:
C1, C2: 33pF
C3, C4, C5: 10nF
J1: terminal
J2: factory setup
J3: RS485
J4: TTL comm
R1: R_Small
RN1: 10k; R_Array_SIP5
U1: AT89C4051-24P; DIP-20_W7.62mm
U2: SN75176AP; DIP-8_W7.62mm
U3: FM24C64B; SOIC-8_3.9x4.9mm_P1.27mm
Y1: 11.059MHz

Connections:
+5V: C3.2, C4.2, C5.2, RN1.1 (common), U1.20 (VCC), U2.8 (VCC), U3.8 (VDD)
D00: RN1.5 (R4), U1.12 (P1.0)
D01: RN1.4 (R3), U1.13 (P1.1)
D02: U1.14 (P1.2)
D03: U1.15 (P1.3)
D04: U1.16 (P1.4)
D05: U1.17 (P1.5)
D06: U1.18 (P1.6)
D07: U1.19 (P1.7)
DE: U1.9 (P3.5), U2.2 (~RE), U2.3 (DE)
FS: J2.1, U1.8 (P3.4)
GND: C1.2, C2.2, C3.1, C4.1, C5.1, J2.2, J4.3, U1.1 (RST/VPP), U1.10 (GND), U2.5 (GND), U3.1 (A0), U3.2 (A1), U3.3 (A2), U3.4 (VSS)
unnamed: C1.1, U1.5 (XTAL1), Y1.1
unnamed: C2.1, U1.4 (XTAL2), Y1.2
unnamed: J1.1, R1.1
unnamed: J1.2, J3.2, U2.6 (A)
unnamed: J3.1, R1.2, U2.7 (B)
RX: J4.1, U1.2 (P3.0), U2.1 (R)
SCL: RN1.2 (R1), U1.7 (P3.3), U3.6 (SCL)
SDA: RN1.3 (R2), U1.6 (P3.2), U3.5 (SDA)
TX: J4.2, U1.3 (P3.1), U2.4 (D)

Notes on the sheet:
buck
A B
