KALTCHUK/Z80_Modular_Computer/KiCAD files/PLC cards/DO-08/untitled.kicad_sch

## KiCad design KiCAD files/PLC cards/DO-08/untitled.kicad_sch (2022-10-09)

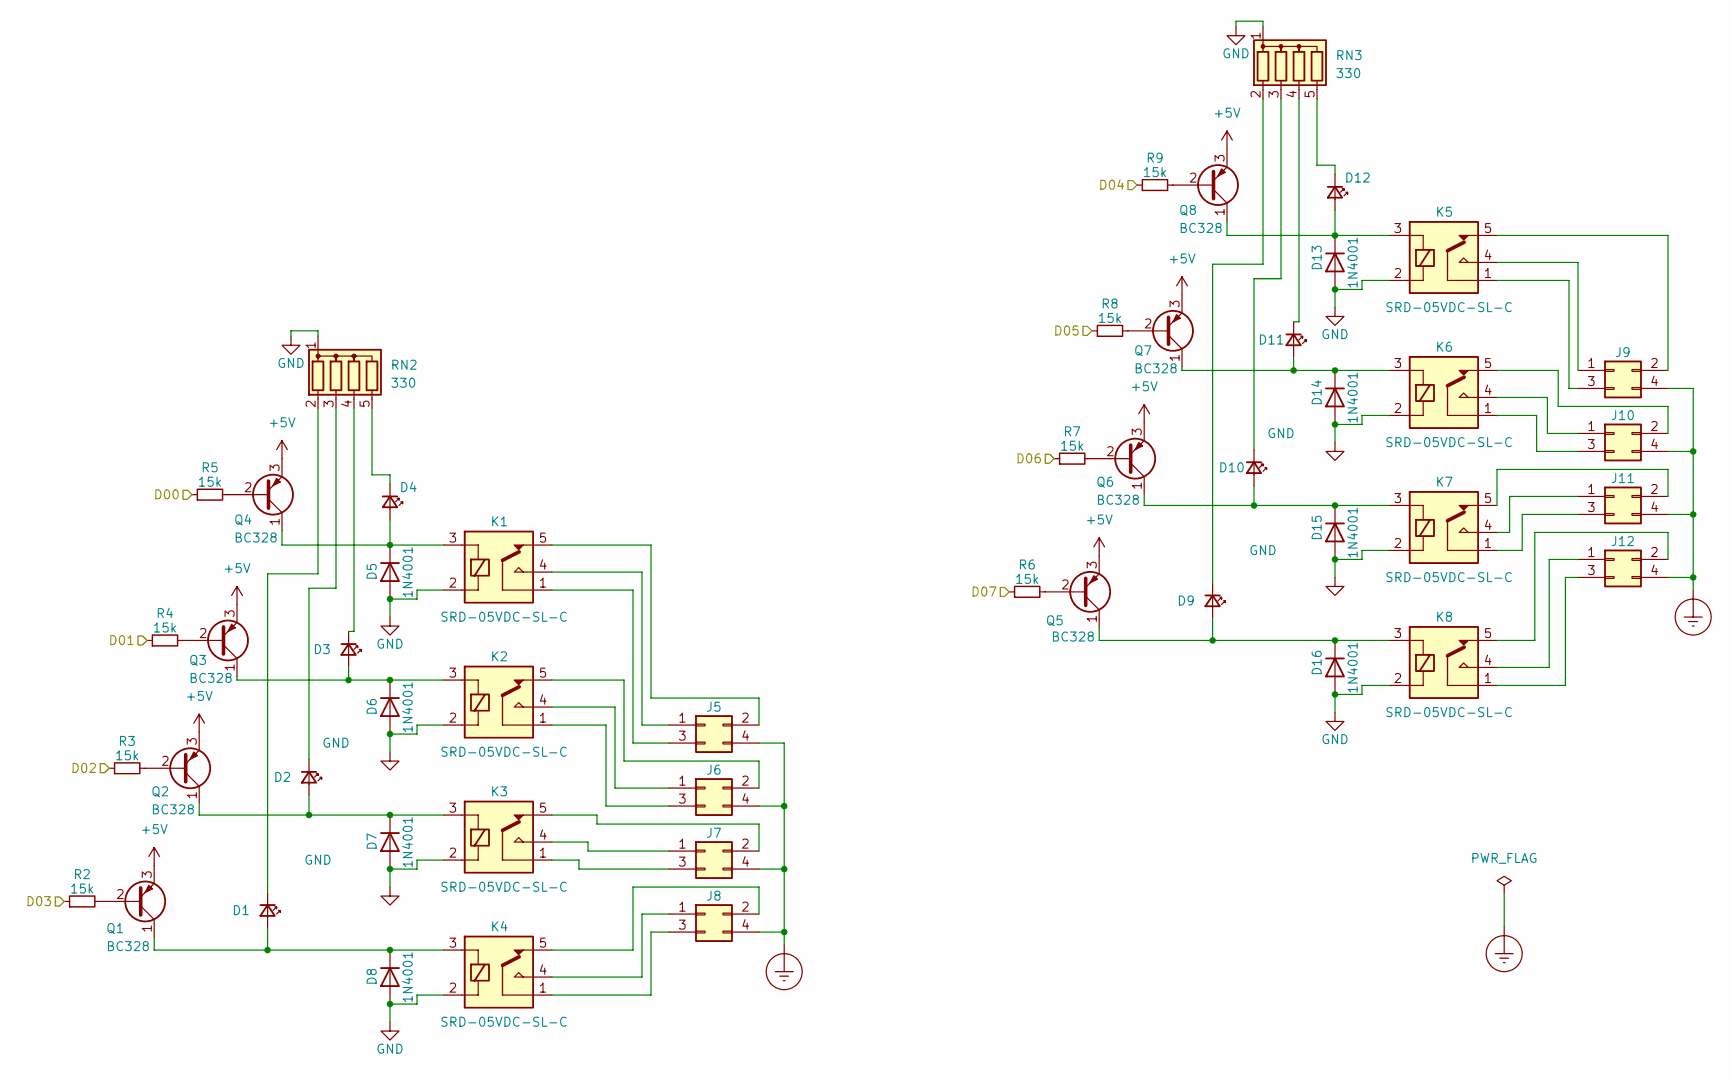
[picture p61: schematic untitled.kicad_sch]

Parts:
D1, D2, D3, D4, D9, D10, D11, D12: LED_Small
D5, D6, D7, D8, D13, D14, D15, D16: 1N4001; D_DO-41_SOD81_P10.16mm_Horizontal
J5, J6, J7, J8, J9, J10, J11, J12: Conn_02x02_Odd_Even
K1, K2, K3, K4, K5, K6, K7, K8: SRD-05VDC-SL-C; Relay_SPDT_Songel-15x19mm
Q1, Q2, Q3, Q4, Q5, Q6, Q7, Q8: BC328; TO-92_Inline
R2, R3, R4, R5, R6, R7, R8, R9: 15k
RN2, RN3: 330; R_Array_SIP5

Connections:
+5V: Q1.3 (E), Q2.3 (E), Q3.3 (E), Q4.3 (E), Q5.3 (E), Q6.3 (E), Q7.3 (E), Q8.3 (E)
D00: R5.1
D01: R4.1
D02: R3.1
D03: R2.1
D04: R9.1
D05: R8.1
D06: R7.1
D07: R6.1
Earth_Protective: J5.4, J6.4, J7.4, J8.4, J9.4, J10.4, J11.4, J12.4
GND: D5.2 (A), D6.2 (A), D7.2 (A), D8.2 (A), D13.2 (A), D14.2 (A), D15.2 (A), D16.2 (A), K1.2, K2.2, K3.2, K4.2, K5.2, K6.2, K7.2, K8.2, RN2.1 (common), RN3.1 (common)
unnamed: D1.1 (K), RN2.2 (R1)
unnamed: D1.2 (A), D8.1 (K), K4.3, Q1.1 (C)
unnamed: D2.1 (K), RN2.3 (R2)
unnamed: D2.2 (A), D7.1 (K), K3.3, Q2.1 (C)
unnamed: D3.1 (K), RN2.4 (R3)
unnamed: D3.2 (A), D6.1 (K), K2.3, Q3.1 (C)
unnamed: D4.1 (K), RN2.5 (R4)
unnamed: D4.2 (A), D5.1 (K), K1.3, Q4.1 (C)
unnamed: D9.1 (K), RN3.2 (R1)
unnamed: D10.1 (K), RN3.3 (R2)
unnamed: D10.2 (A), D15.1 (K), K7.3, Q6.1 (C)
unnamed: D11.1 (K), RN3.4 (R3)
unnamed: D11.2 (A), D14.1 (K), K6.3, Q7.1 (C)
unnamed: D12.1 (K), RN3.5 (R4)
unnamed: D12.2 (A), D13.1 (K), K5.3, Q8.1 (C)
unnamed: D9.2 (A), D16.1 (K), K8.3, Q5.1 (C)
unnamed: J5.1, K1.4
unnamed: J5.2, K1.5
unnamed: J5.3, K1.1
unnamed: J6.1, K2.4
unnamed: J6.2, K2.5
unnamed: J6.3, K2.1
unnamed: J7.1, K3.4
unnamed: J7.2, K3.5
unnamed: J7.3, K3.1
unnamed: J8.1, K4.4
unnamed: J8.2, K4.5
unnamed: J8.3, K4.1
unnamed: J9.1, K5.4
unnamed: J9.2, K5.5
unnamed: J9.3, K5.1
unnamed: J10.1, K6.4
unnamed: J10.2, K6.5
unnamed: J10.3, K6.1
unnamed: J11.1, K7.4
unnamed: J11.2, K7.5
unnamed: J11.3, K7.1
unnamed: J12.1, K8.4
unnamed: J12.2, K8.5
unnamed: J12.3, K8.1
unnamed: Q1.2 (B), R2.2
unnamed: Q2.2 (B), R3.2
unnamed: Q3.2 (B), R4.2
unnamed: Q4.2 (B), R5.2
unnamed: Q5.2 (B), R6.2
unnamed: Q6.2 (B), R7.2
unnamed: Q7.2 (B), R8.2
unnamed: Q8.2 (B), R9.2
