KALTCHUK/Z80_Modular_Computer/Ride7/DO-8/ModbusSlave.h

/*
 ModbusSlave.h - Header file for 2 modbus remote I/O cards - DI-16 (16 digital inputs) and DO-8 (8 digital outputs).

 DO-8 has 8 coils (registers 1 to 8) and 2 holding registers for baud rate (register 40001) and slave ID (register 40002).
 DI-16 has 16 discrete inputs (registers 10001 to 10016) and 2 holding registers for baud rate (register 40001) and slave ID (register 40002).
 
 Port1 is connected to the I/O bus. P1.0 and P1.1 need external pullup resistors.

 Port3 has a few especial pins:
	P3.4: FS (use factory set id and baud rate if signal low)
	P3.5: DE (RS485 drive enable)
	P3.7: SEL (select lower or upper word for digital input)

*/

// Definitions
#define _SEL        RD	    // SEL pin (P3.7)
#define _DE         T1      // DE pin (P3.5)
#define _FS         T0      // FS pin (P3.4)

#define MAXBUF	24

// Global Variables
char buf[MAXBUF];
char numCoils;
char numDiscreteInputs;
char numHoldingRegisters;

unsigned int charTimeout;
unsigned int frameTimeout;

unsigned int milli;
unsigned int id;

char outputState=0;         // outputState is the inverse of P1

// Function Prototyping
void milliStart(void);
void modbusBegin(unsigned int baud);
void modbusPoll(void);
char boolRead(unsigned int startAddress);
long wordRead(unsigned int startAddress);
bit coilWrite(unsigned int startAddress, unsigned int value);
bit holdingRegisterWrite(unsigned int startAddress, unsigned int value);
void oops(int errCode);
void write(char len);
unsigned int crc(char len);
unsigned int div8RndUp(unsigned int value);
unsigned int bytesToWord(char high, char low);

void timer0_isr() interrupt 1
{
    TH0 = 0xfc;        //Reload the TIMER0.
    TL0 = 0x66;

    milli++;
}

void milliStart(void) {
	ET0 = 0;            //Disable TIMER0 interrupt while configuring it.
    TMOD |= 0x01;      //TIMER0 = mode_1.
    TH0 = 0xfc;        //Load the timer value for 1ms tick (crystal = 11.059MHz).
    TL0 = 0x66;
    TR0 = 1;           //Turn ON TIMER0.
    ET0 = 1;           //Enable TIMER0 Interrupt.
    EA = 1;            //Enable Global Interrupt.
	
	milli = 0;
}

void modbusBegin(unsigned int baud) {
    milliStart();

    if (baud >= 19200) {
        charTimeout = 1;
        frameTimeout = 2;
    }
    else {
        charTimeout = (19200/baud) +1;
        frameTimeout = charTimeout*2;
//        charTimeout = 15000/baud;		// in the range [1; 13]
//        frameTimeout = 35000/baud;		// in the range [2; 30]
    }
  
    do {
        if (RI != 0) {
            milliStart();
            RI = 0;
        }
    } while (milli < frameTimeout);
}

void modbusPoll() {
    char i = 0, j;
    unsigned int startAddress, quantity;
    long value;

    if (RI != 0) {
        do {
            if (RI != 0) {
                milliStart();
                if(i < MAXBUF)	buf[i] = serialRX();
                else			RI = 0 ;
                i++;
            }
        } while (milli < charTimeout && i < MAXBUF);
	
        while (milli < frameTimeout) {
            RI = 0;
        }

        if (RI == 0 && (buf[0] == id || buf[0] == 0) && i < MAXBUF) {
            if (crc(i - 2) != bytesToWord(buf[i - 1], buf[i - 2])) return;
        
            switch (buf[1]) {
            case 1: /* Read Coils */
                startAddress = bytesToWord(buf[2], buf[3]);
                quantity = bytesToWord(buf[4], buf[5]);
                if (quantity == 0 || quantity > 8)                    oops(3);
                else if ((startAddress + quantity) > numCoils)        oops(2);
                else {
                    for (j = 0; j < quantity; j++) {
                        value = boolRead(startAddress + j);
                        if (value > 1) {
                            oops(4);
                            return;
                        }
                        if (value == 1)     buf[3 + (j >> 3)] |= 1<<(j & 7);
                        else				buf[3 + (j >> 3)] &= ~(1<<(j & 7));
                    }
                    buf[2] = div8RndUp(quantity);
                    write(3 + buf[2]);
                }
                break;
        
            case 3: /* Read Holding Registers */
                startAddress = bytesToWord(buf[2], buf[3]);
                quantity = bytesToWord(buf[4], buf[5]);
                if (quantity == 0 || quantity > numHoldingRegisters)          oops(3);
                else if ((startAddress + quantity) > numHoldingRegisters)     oops(2);
                else {
                    for (j = 0; j < quantity; j++) {
                        value = wordRead(startAddress + j);
                        if (value < 0) {
                            oops(4);
                            return;
                        }
                        buf[3 + (j * 2)] = (char)(value >> 8);
                        buf[4 + (j * 2)] = (char)(value & 0x00ff);
                    }
                    buf[2] = quantity * 2;
                    write(3 + buf[2]);
                }
                break;

            case 5: /* Write Single Coil */
                startAddress = bytesToWord(buf[2], buf[3]);
                value = bytesToWord(buf[4], buf[5]);
                if (value != 0 && value != 0xff00)          oops(3);
                else if (startAddress >= numCoils)          oops(2);
                else if (!coilWrite(startAddress, value))   oops(4);
                else write(6);
                break;
 
            case 6: /* Write Single Holding Register */
                startAddress = bytesToWord(buf[2], buf[3]);
                value = bytesToWord(buf[4], buf[5]);
                if (startAddress >= numHoldingRegisters)                oops(2);
                else if (!holdingRegisterWrite(startAddress, value))    oops(4);
                else write(6);
                break;
            
            case 15: /* Write Multiple Coils */
                startAddress = bytesToWord(buf[2], buf[3]);
                quantity = bytesToWord(buf[4], buf[5]);
                if (quantity == 0 || quantity > ((MAXBUF - 10) << 3) || buf[6] != div8RndUp(quantity))  oops(3);
                else if ((startAddress + quantity) > numCoils)                                          oops(2);
                else {
                    for (j = 0; j < quantity; j++) {
                        value = buf[7 + (j >> 3)] & (1<<(j & 7));
                        if (value != 0)	value = 0xff00;
                        if (!coilWrite(startAddress + j, value)) {
                            oops(4);
                            return;
                        }
                    }
                    write(6);
                }
                break;

            case 16: /* Write Multiple Holding Registers */
                startAddress = bytesToWord(buf[2], buf[3]);
                quantity = bytesToWord(buf[4], buf[5]);
                if (quantity == 0 || quantity > ((MAXBUF - 10) >> 1) || buf[6] != (quantity * 2))   oops(3);
                else if (startAddress + quantity > numHoldingRegisters)                             oops(2);
                else {
                    for (j = 0; j < quantity; j++) {
                        if (!holdingRegisterWrite(startAddress + j, bytesToWord(buf[j * 2 + 7], buf[j * 2 + 8]))) {
                        oops(4);
                        return;
                        }
                    }
                    write(6);
                }
                break;

            default:
                oops(1);
                break;
            }
        }
    }
}

char boolRead(unsigned int startAddress) {  // 1=ON, 0=OFF, 2=error.
    char boolStatus;

    if (startAddress > (numCoils - 1))   return 2;
    boolStatus = outputState & (1 << startAddress);
    if (boolStatus != 0)    boolStatus = 1;
    return boolStatus;
}

long wordRead(unsigned int startAddress) {
	if (startAddress > (numHoldingRegisters - 1))   return -1;
    return EEPROMread(startAddress);
}

bit coilWrite(unsigned int startAddress, unsigned int value) {
    if (startAddress > (numCoils - 1))   return 0;
    if (value == 0)     outputState &= ~(1 << startAddress);
    else                outputState |= (1 << startAddress);
    P1 = ~outputState;
    return 1;
}

bit holdingRegisterWrite(unsigned int startAddress, unsigned int value) {
	if (startAddress > (numHoldingRegisters - 1))   return 0;
    EEPROMwrite(startAddress, value);
    return 1;
}

void oops(int errCode) {
    buf[1] |= 0x80;
    buf[2] = (char)errCode;
    write(3);
}

void write(char len) {
    char i;
    unsigned int CRC;

    if (buf[0] != 0) {
        CRC = crc(len);
	
        buf[len] = (char)(CRC & 0x00ff);
        buf[len + 1] = (char)(CRC >> 8);

        _DE = 1;
        for(i=0; i < len+2; i++)	serialTX(buf[i]);
        _DE = 0;
    }
}

unsigned int crc(char len) {
  bit lsb;
  char i, j;
  unsigned int crc = 0xFFFF;

  for (i = 0; i < len; i++) {
    crc ^= (unsigned int)buf[i];
    for (j = 0; j < 8; j++) {
      lsb = crc & 1;
      crc >>= 1;
      if (lsb == 1) {
        crc ^= 0xA001;
      }
    }
  }
  return crc;
}

unsigned int div8RndUp(unsigned int value) {
  return (value + 7) >> 3;
}

unsigned int bytesToWord(char high, char low) {
  return (high << 8) | low;
}
