KALTCHUK/Z80_Modular_Computer/Ride7/DO-8/DO-8.c

/*
 DO-8.c - Modbus RTU Slave controller (AT89C4051) for DO-8 Card. By Kaltchuk, Sep/2022.
*/

#include <REG51.h>
#include "Serial.h"
#include "EEPROM.h"
#include "ModbusSlave.h"

void main() {
	numCoils = 8;
	numDiscreteInputs = 0;
	numHoldingRegisters = 4;

    _DE = 0;

    baud = 19200;	// factory set baud rate.
	id = 1;			// factory set modbus slave id.

	if (_FS == 1) {
		baud = EEPROMread(0);
		id =  EEPROMread(1);
	}
	serialInit(baud);
	modbusBegin(baud);
	
	while (1) {
        modbusPoll();
	}
}
