KALTCHUK/Z80_Modular_Computer/Arduino scripts/i2c_finder/i2c_finder.ino

#include <Wire.h>

void setup()
{
  Wire.begin();

  Serial.begin(9600);
}

void loop()
{
  int error;
  int address;
  int devices = 0;

  Serial.println("Devices found:");

  for(address = 1; address < 127; address++ ) 
  {
    Wire.beginTransmission(address);
    error = Wire.endTransmission();

    if (error == 0)
    {
      Serial.print("0x");
      if (address<16) 
        Serial.print("0");
      Serial.println(address,HEX);
      devices++;
    }
    
    else if (error==4) 
    {
      Serial.print("Unknown error at address 0x");
      if (address<16) 
        Serial.print("0");
      Serial.println(address,HEX);
    }    
  }
  
  if (devices == 0)
    Serial.println("No I2C devices found");

  delay(5000);           
}
