KALTCHUK/Z80_Modular_Computer/Python/commtest.py

#************************************************************************************************
# This program sends 1 or more files to CP/M. The files must be in the same directory as SEND.PY.
#************************************************************************************************
import serial

STX = 0x2
EOT	= 0x4
ACK	= 0x6
LF	= 0xA
CR	= 0xD
NAK	= 0x15
Ctrl_C = 0x3

print('\r\n')    

# Which COM port?
#com_port = input("COM port number? ")
com_port = 16
Z80_port = serial.Serial(port = "COM" + str(com_port), baudrate = 9600, timeout = 5)
Z80_port.flushInput()

# Start RECEIVE.COM on CP/M
print('Starting RECEIVE.COM on CP/M...')
Z80_port.write(b'LCDECHO')
Z80_port.write(b'\r')
Z80_port.write(STX)
Z80_port.write(EOT)
Z80_port.write(Ctrl_C)
exit()




# Wait for <ACK>
#print('Waiting for ACK...')
#rec_byte = Z80_port.read(1)
#if rec_byte != ACK:
#    print('No ACK. Transmisson aborted.'+'\r\n')
#    Z80_port.close()
#    exit()

all_drives = "ABCDEFGHIJKLMNOP"
while True:
    listFCB = list("            ") 

    # Which drive?
    while True:
        drive = input("Target drive in CP/M (A through P)?").upper()
        if drive[0] in all_drives:
            break
    listFCB[0] = drive[0]

    # Which file?
    while True:
        file_name = input("File name? ").upper()
        if len(file_name) >= 1:
            break

    # Transform drive + file_name into FCB format
    dot = file_name.find(".")
    i = 1
    if dot == -1:                               # name has no extension
        while i < 9:
            if (len(file_name) >= i):
                listFCB[i] = file_name[i-1]
            else:
                for i in range(i, 8):
                    listFCB[i] = " "
            i+=1
        while i < 12:
            listFCB[i] = " "
            i+=1
    else:                                       # name has extension
        while i < 9:
            if i <= dot:
                listFCB[i] = file_name[i-1]
            else:
                listFCB[i] = " "
            i+=1
        while i < 12:
            if len(file_name) >= (dot+i-7):
                listFCB[i] = file_name[dot+i-8]
            else:
                listFCB[i] = " "
            i+=1

    # Send FCB
    print('Sending FCB...')
    FCB = ''.join(listFCB)
    Z80_port.write(FCB.encode())
    
    # Send CTRL-C to end execution of LCDecho on CP/M
    Z80_port.write(Ctrl_C)
    exit()
    
    # Wait for <ACK>
    print('Waiting for ACK...')
    while True:
        rec_byte = Z80_port.read(1)
        if rec_byte == ACK:
            break

    # Send EOT
    Z80_port.write(EOT)

    # Send checksum
    print('\r\n' + 'Sending Checksum...')
    msn = CheckSum // 16
    if msn < 0xa:
        msn += 0x30
    else:
        msn += 0x37
    lsn = CheckSum % 16
    if lsn < 0xa:
        lsn += 0x30
    else:
        lsn += 0x37
    Z80_port.write(msn.to_bytes(1, 'big'))
    Z80_port.write(lsn.to_bytes(1, 'big'))

    # Wait for ACK or NAK
    print('Waiting for ACK or NAK...')
    rec_byte = Z80_port.read(1)
    if rec_byte == ACK:
        print('Transmission successful.')
    elif rec_byte == NAK:
        print('Houston, we had a problem.')
    else:
        print('No answer from RECEIVE.')
        break

    # Xmit another file?
    more = input('Transmit another file? (y or n)')
    if more.upper() != 'Y':
        # Send STX to restart the receiving process
        Z80_port.write(STX)
    else:
        # Send ACK to release RECEIVE and return command to CCP
        Z80_port.write(ACK)
        break

print('\r\n')    
Z80_port.close()
